redstoner-35/DFEx-FarBeaMon3tr/img/驱动仓去氧化后.jpg

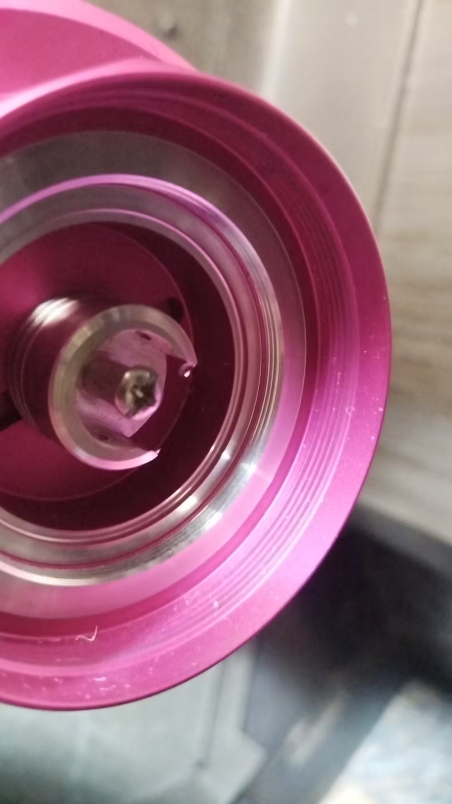
img/驱动仓去氧化后.jpg
