redstoner-35/DFEx-FarBeaMon3tr/机械/电池架/Step/电池架均衡和充电板空隙垫圈.STEP

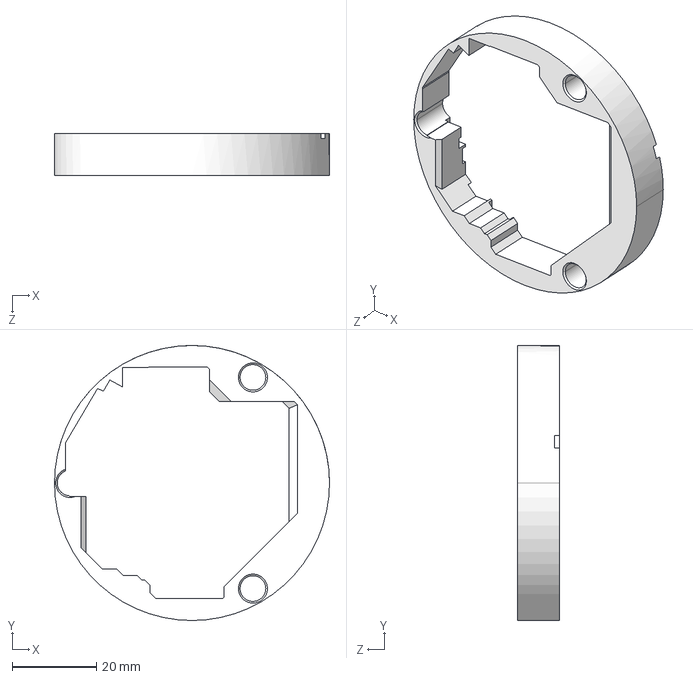
[picture p48: CAD file, 2025-11-03]
机械/电池架/Step/电池架均衡和充电板空隙垫圈.STEP
65.4 x 65.4 x 10.0 mm
