redstoner-35/DFEx-FarBeaMon3tr/机械/电池架/电池架正极黄铜导电电极.SLDPRT

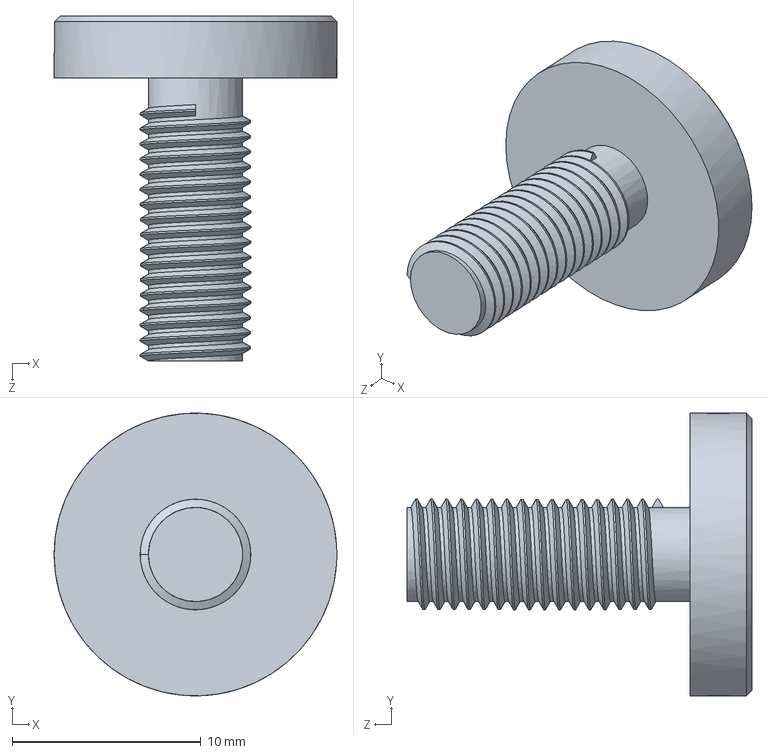
[picture p49: CAD file, 2025-05-08]
机械/电池架/电池架正极黄铜导电电极.SLDPRT
15.0 x 15.0 x 18.3 mm
