redstoner-35/DFEx-FarBeaMon3tr/机械/筒身/Step/电池仓尾盖.stp

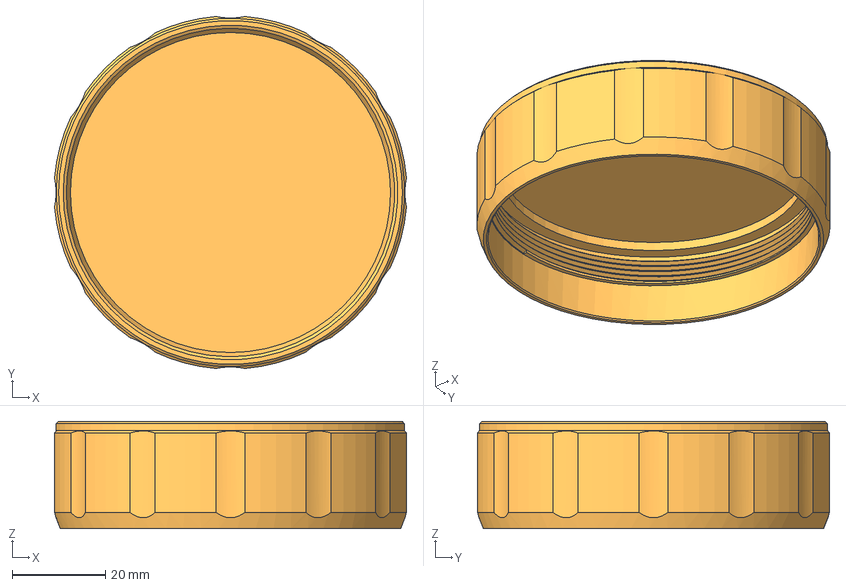
[picture p50: CAD file, 2025-05-15]
机械/筒身/Step/电池仓尾盖.stp
75.4 x 75.4 x 23.0 mm
