redstoner-35/DFEx-FarBeaMon3tr/机械/光学部分/定位片3D制造文件/专用定位片-7070灯珠.3mf

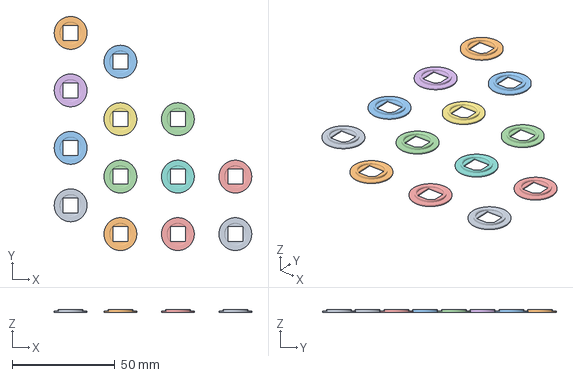
[picture p52: CAD file, 2025-07-03]
机械/光学部分/定位片3D制造文件/专用定位片-7070灯珠.3mf
96.2 x 114.0 x 1.50 mm
专用定位片-7070-PA6GF.STEP x 13
