redstoner-35/DFEx-FarBeaMon3tr/机械/电池架/Step/电池正极铜垫片.STEP

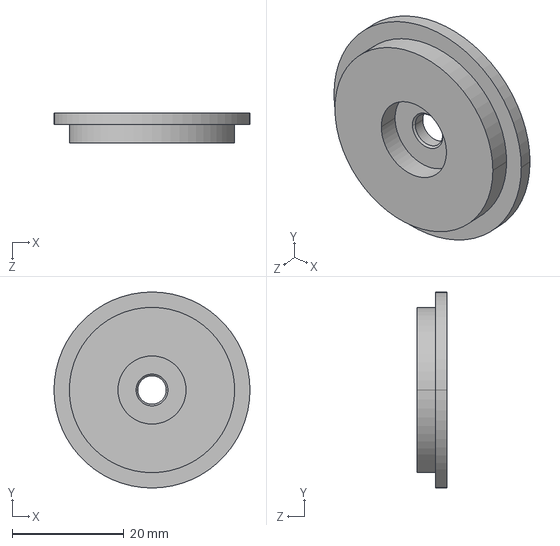
[picture p53: CAD file, 2025-11-03]
机械/电池架/Step/电池正极铜垫片.STEP
35.1 x 35.1 x 5.40 mm
