redstoner-35/DFEx-FarBeaMon3tr/机械/电池架/电池架装配效果.SLDPRT

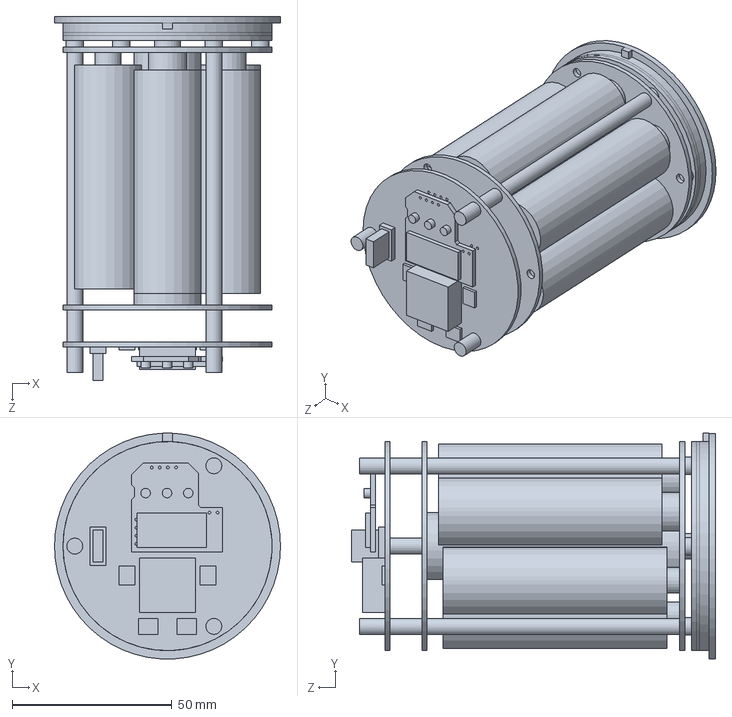
[picture p54: CAD file, 2025-05-08]
机械/电池架/电池架装配效果.SLDPRT
70.7 x 70.6 x 113.9 mm
