redstoner-35/DFEx-FarBeaMon3tr/机械/筒身/Step/电池仓前盖.stp

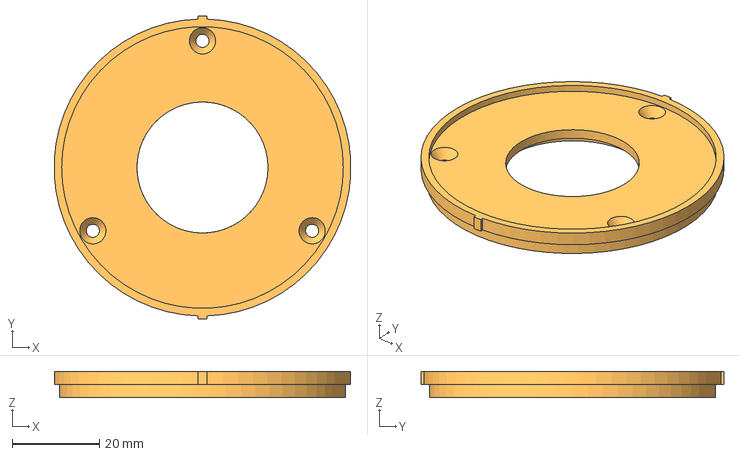
[picture p55: CAD file, 2025-05-15]
机械/筒身/Step/电池仓前盖.stp
67.9 x 69.4 x 6.00 mm
