redstoner-35/DFEx-FarBeaMon3tr/机械/风扇手柄外框/Step/40风扇不锈钢夹片-改版.STEP

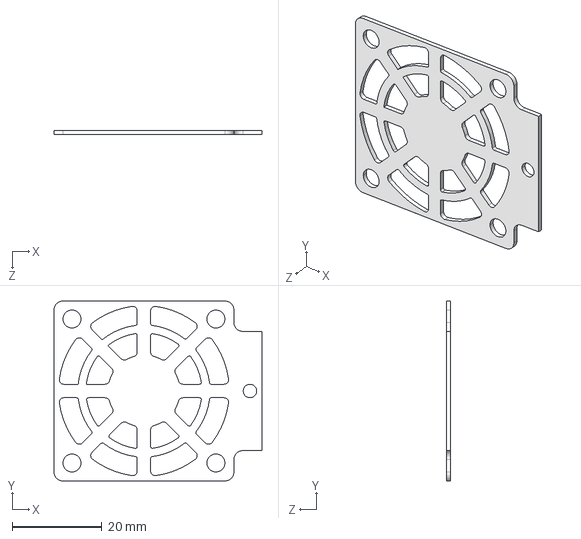
[picture p56: CAD file, 2025-11-03]
机械/风扇手柄外框/Step/40风扇不锈钢夹片-改版.STEP
46.2 x 40.0 x 1.00 mm
