redstoner-35/DFEx-FarBeaMon3tr/机械/筒身/Step/电池仓尾部显示面板.stp

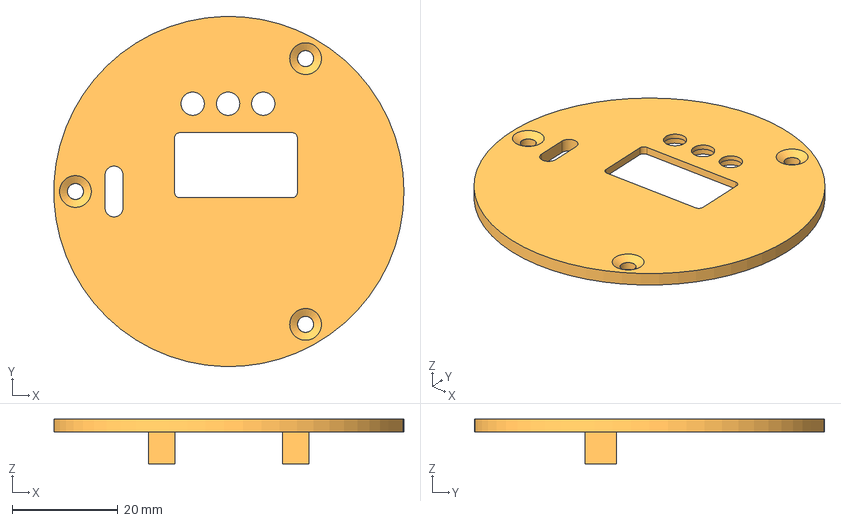
[picture p57: CAD file, 2025-05-15]
机械/筒身/Step/电池仓尾部显示面板.stp
66.2 x 66.2 x 8.50 mm
