redstoner-35/DFEx-FarBeaMon3tr/机械/风扇手柄外框/Step/40风扇外框23日.STEP

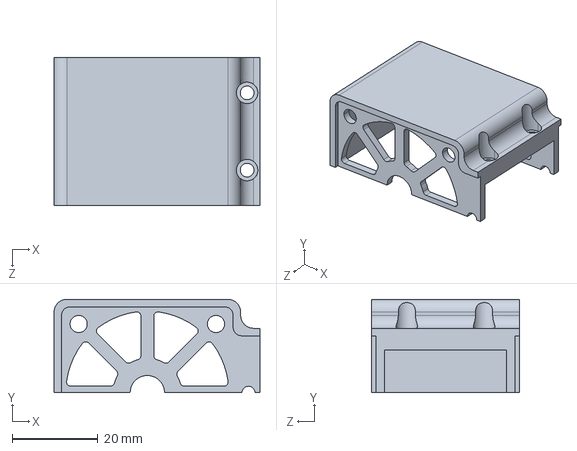
[picture p58: CAD file, 2025-11-03]
机械/风扇手柄外框/Step/40风扇外框23日.STEP
48.0 x 21.8 x 34.5 mm
