redstoner-35/DFEx-FarBeaMon3tr/机械/电池架/Step/电池架中心柱.STEP

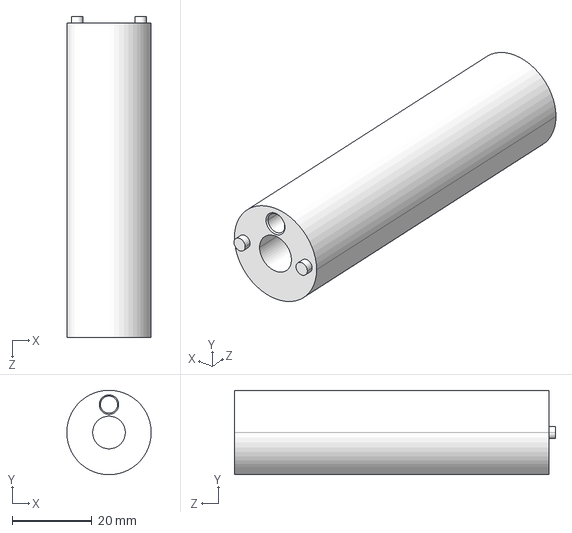
[picture p59: CAD file, 2025-05-08]
机械/电池架/Step/电池架中心柱.STEP
21.2 x 21.2 x 80.6 mm
