redstoner-35/DFEx-FarBeaMon3tr/固件/电池棒控制器固件/User/main.c

#include "ht32.h"
#include "delay.h"
#include "LCD_Init.h"
#include "lcd.h"
#include "ADC.h"
#include "I2C.h"
#include "Key.h"
#include "GUI.h"
#include "Config.h"
#include "CapTest.h"
#include "LogSystem.h"
#include "WatchDog.h"
#include "BalanceMgmt.h"
#include "AUXPSU.h"

//函数声明
void PowerMgmtSetup(void);
void KickIP2366ToWakeUp(void);
void IP2366_PreInit(void);
void IP2366_Telem(void);
void IP2366_PostInit(void);
void UpdateIfSysCanOFF(void);
void DetectIfIP2366Reset(void);
void EnteredInstantCapTest(void);
void PowermanagementSleepControl(void);
void CTestAverageACC(void);
void CTestFSMHandler(void);
void SysOverHeatProt(void);
void TCResetFSM(void);
void ApplyScreenDirection(void);
void IP2366_ReConfigOutWhenTypeCOFF(void);
void CheckForFlashLock(void);
void SetDebugPortState(bool IsEnable);
void AttackTimeCounter(void);
void PushDefaultResultToVBat(void);
void OverChargeDetectModule(void);
void HPPowerGuage_Start(void);
void AutoBalTIMHandler(void);
void AdapEmuTIMHandler(void);
void SysAutoSavePowerCfg(void);
void DynamicUpdateSinkPower(void);

//常量
bool SensorRefreshFlag=false;

int main(void)
 {
 //初始化系统时钟
 CKCU_PeripClockConfig_TypeDef CLKConfig={{0}};
 CLKConfig.Bit.PA=1;
 CLKConfig.Bit.PB=1;
 CLKConfig.Bit.PC=1;
 CLKConfig.Bit.AFIO=1;
 CLKConfig.Bit.ADC=1;
 CLKConfig.Bit.EXTI=1;
 CLKConfig.Bit.SPI0 = 1;
 CLKConfig.Bit.PDMA = 1;
 CLKConfig.Bit.WDT = 1;
 CLKConfig.Bit.BKP = 1;
 CKCU_PeripClockConfig(CLKConfig,ENABLE);
 //启动SYSTICK和电源锁定引脚
 #ifndef EnableDebugMode
 SetDebugPortState(false);
 #endif
 delay_init(); //对延时函数的运行环境进行初始化 
 PowerMgmtSetup(); //进行自举
 //底层外设初始化
 LCD_HardwareInit();
 LCD_Init(); //进行LCD的硬件初始化和寄存器初始化
 PostScreenInit(); //显示自检的初始主界面
 LCD_EnableBackLight(); //启动LCD背光，LCD开始显示
 //开始图形化自检
 EnableHBTimer(); //初始化系统8Hz心跳定时器
 SideKey_Init(); //侧按初始化 	
 InternalADC_Init(); //ADC初始化 
 KickIP2366ToWakeUp(); //踢一脚2366唤醒
 SMBUS_Init(); //启动SMBUS
 IP2366_PreInit(); //进行2368初步配置关闭充放电，读取寄存器后再开
 LoadConfig(); //读取系统配置
 CheckIfHBTIMStart(); //检查心跳定时器是否启动
 CheckForFlashLock(); //给存储器上锁永久禁止读取
 POR_ReadCapData(); //读取测容数据
 BalanceMgmt_Init(); //配置均衡控制器
 RunLogModule_POR(); //读取数据
 ApplyScreenDirection(); //应用屏幕方向
 IP2366_PostInit(); //IP2366应用后配置
 HPPowerGuage_Start(); //初始化高精度功率计
 PushDefaultResultToVBat(); //将电池电压数据默认应用给结构体进行显示
 EnteredInstantCapTest(); //尝试进入测试菜单
 AUXPSU_DetectIfCPortTriggerPresent(); //检测C口诱骗硬件是否存在
 //自检完毕，进入系统
 ShowPostInfo(100,"系统初始化完成",(char *)QueryPostDoneID(),Msg_POSTOK);
 delay_ms(!CfgData.EnableFastBoot?400:150); //关闭快速启动则多延时一会让人可以看清
 ClearScreen();
 //根据设置，执行菜单切换
 if(CfgData.InstantCTest==InstantCTest_EnteredOK)SwitchingMenu(&CapTestMenu); //一次性测容条件满足直接进入测容菜单
 else SwitchingMenu(CfgData.EnableLargeMenu?&LargeMainMenu:&MainMenu);        //否则切换到主菜单
 SensorRefreshFlag=false; //清除flag
 #ifndef EnableDebugMode
 WatchDog_Init(); //启动看门狗
 #endif
 //主循环
 while(1)
   {
	 //实时处理任务
	 ADC_GetResult(); 
	 SideKey_LogicHandler(); 
	 CTestFSMHandler(); //测容状态机处理
	 PowermanagementSleepControl(); //睡眠管理
	 SysOverHeatProt(); //过热保护处理
	 MenuRenderProcess(); //执行菜单渲染 
	 //125ms定时处理的入口和喂狗检测
	 if(!SensorRefreshFlag)continue;
	 #ifndef EnableDebugMode
	 WatchDog_Feed(); //喂狗
	 #endif
	 //进行其余125ms定时处理
	 AutoBalTIMHandler(); //自动均衡计时器
	 Balance_IOMgmt(); //进行均衡器的控制
	 SideKey_TIMCallback(); 
	 DynamicUpdateSinkPower(); //动态更新输入功率
	 UpdateIfSysCanOFF(); //更新系统是否可以关闭
	 IP2366_Telem(); //每0.125秒获取一次2366的状态
	 CTestAverageACC(); //测容系统遥测
	 UpdataRunTimeLog(); //更新日志
	 SysAutoSavePowerCfg(); //自动省电功能
	 OverChargeDetectModule(); //过充检测
	 DetectIfIP2366Reset(); //监测IP2366是否复位
	 GUIDelayHandler(); //GUI延时处理
	 AdapEmuTIMHandler(); //适配器模拟计时器处理
	 IP2366_ReConfigOutWhenTypeCOFF(); //从VBUS起来的重新连接
	 AUXPSU_Mgmt(); //进行辅助电源的配置
	 IntEditMenuKeyEffHandler(); //实现按下特效
	 TCResetFSM(); //实现Type-C重连
	 AttackTimeCounter(); //防止爆破攻击的保护
	 SensorRefreshFlag=false;
	 }
 return 0;
 }
