redstoner-35/DFEx-FarBeaMon3tr/固件/电池棒控制器固件/POST/IP2366_Init.c

#include "IP2366_REG.h"
#include "lcd.h"
#include "GUI.h"
#include "Config.h"
#include "delay.h"
#include "ADC.h"
#include "BalanceMgmt.h"
#include <string.h>
#include <math.h>
#include "AUXPSU.h"
#include "WatchDog.h"
#include "LogSystem.h"

typedef enum
	{
	IP2366DCState_Normal,
	IP2366DCState_LowTemp,
	IP2366DCState_highTemp
	}IP2366DCStateDef;

bool IsEnableDischargeAtStor=true;
static char WaitAfterTypeCRemoved;	
bool CurrentStorDisState=true;
bool IsSystemOverheating=false;
bool IsSystemLowTemp=false;
static IP2366DCStateDef IP2366DCDCState=IP2366DCState_Normal;
static bool IsAutoSaveEnabled=false;
static unsigned char AutoSavePowerTIM=160;
static unsigned char WaitTCReconnectTIM=0;
static unsigned int TCShortDisBlankTIM=0;
static bool IsSinkPowerThermalLimited;
static bool SysChgState; //系统充电状态
static ChargePowerDef CurrentSinkPower;  //当前系统的输入功率
IP2366ResetCPortProcDef IPSinkState=IP2366_CPort_Reseted;

//外部函数
void Force2366ToRestart(void); //强制2366断电重启

//计算存储模式开启时，是否打开放电模块
bool IP2366_IsEnableDischarge(float VBatRaw)
	{
	float VBatt,VbattThres;
	//计算电池电压
  VBatt=VBatRaw/BattCellCount;
	VBatt*=1000; //转mV
	//计算触发阈值
	VbattThres=3500+((float)StorageMode*100);
	//进行施密特处理
  if(VBatt>VbattThres+100)IsEnableDischargeAtStor=true;
	else if(VBatt<=VbattThres)IsEnableDischargeAtStor=false;
	//返回结果
	return IsEnableDischargeAtStor;
	}	

//内部函数，负责根据系统当前温度运算充电功率
bool UpdateSinkPower(bool IsForceUpdate)
	{
	ChargePowerDef Buf;
	//系统不支持返回true
	if(!CurrentIP2366FW->ExtendedTCSetting)return true;
	//关闭输入自适应Sink功能，强制使用指定的Sink Power
	if(!CfgData.EnableSmartSinkPower)Buf=CfgData.MaxSnkPower;
	//温度监视系统故障，使用最低的充电功率
	else if(!ADCO.IsNTCOK)Buf=Power_30W;
	//温度监视系统正常，按照温度值选择充电功率
	else if(ADCO.Systemp<42)Buf=Power_140W;
	else if(ADCO.Systemp<45)Buf=Power_100W;
	else if(ADCO.Systemp<48)Buf=Power_65W;
	else if(ADCO.Systemp<52)Buf=Power_60W;
	else if(ADCO.Systemp<55)Buf=Power_45W;
	else Buf=Power_30W;
	//判断当前系统设置是否小于算出来的充电功率，如果小于则override为系统设置
	if(Buf>CfgData.MaxSnkPower)Buf=CfgData.MaxSnkPower;
	if(IsForceUpdate||CurrentSinkPower!=Buf)	
		{
		//设置充电功率寄存器，成功则同步结果并返回true，否则返回false
		if(IP2366_UpdateSinkPower(Buf))CurrentSinkPower=Buf;
		else return false; 
		}
	//其余情况，返回true
  return true;
	}	
	
//如果系统因为充电开始时过温限制了充电功率，则该模块会尝试在系统回到低温状态后恢复充电功率
void RestoreSinkPower(void)
	{
	float Thres;
	//当前没有使能升功率操作	
	if(!IsSinkPowerThermalLimited)return;
	//根据目标的Sink Power判断触发回升的阈值
	switch(CfgData.MaxSnkPower)
		{
		case Power_140W:Thres=42;break;
		case Power_100W:Thres=45;break;
		case Power_65W:Thres=48;break;
		case Power_60W:Thres=52;break;
		case Power_45W:Thres=55;break;
		case Power_30W:Thres=60;break;
		}
	//如果当前系统温度小于回升阈值，则触发回升
	if(!ADCO.IsNTCOK||ADCO.Systemp>=Thres)return;
	if(UpdateSinkPower(true))IsSinkPowerThermalLimited=false;
	}	
	
//在连接C口后，动态更新输入最大功率
void DynamicUpdateSinkPower(void)
	{
	bool Result;
	BatteryStateDef BattState;
	//系统不支持单独设置Sink输入或者关闭了智能功率协商，不执行
  if(!CurrentIP2366FW->ExtendedTCSetting||!CfgData.EnableSmartSinkPower)return;		
	//检测系统是否连接输入且处于正在充电过程中
	if(!IP2366_GetIfInputConnected())Result=false;
	else if(!IP2366_GetChargerState(&BattState))Result=false;
	else switch(BattState)
		{
		case Batt_ChgWait:
		case Batt_CCCharge:
		case Batt_CVCharge:Result=true;break;
	  //其余情况
		default:Result=false;
		}	
	//C口处于插入状态，执行恢复输入功率的尝试
	if(Result)RestoreSinkPower();
	//定时器递减
	else if(TCShortDisBlankTIM>0)TCShortDisBlankTIM--;
	//检测到用户插入C口后更新充电功率
  if(SysChgState==Result)return;	
	//当前系统拔除C口，不执行充电功率更新，进入消隐阶段短时间内阻止C口断联引起的误判
	if(TCShortDisBlankTIM||!Result)
		{
		TCShortDisBlankTIM=480;
		SysChgState=Result;
		}		
	else 
		{
	  //正常执行更新事件并判断输入功率是否被限制
		if(UpdateSinkPower(false))SysChgState=Result;
	  if(CurrentSinkPower<CfgData.MaxSnkPower)IsSinkPowerThermalLimited=true;
		else IsSinkPowerThermalLimited=false;
		}
	}
	
//IP2366初始化
void IP2366_PreInit(void)
	{
	char i=5;
	char VendorString[6];
	char FWIDReport[32];
	IP2366InputDef ICFG;
	IP2366OutConfigDef OCFG;
	IP2366HWRevDef HWID;
	ShowPostInfo(25,"充电IC初配置","07",Msg_Statu);
	//配置结构体
	ICFG.ChargeCurrent=9700;
	ICFG.ChargePower=Power_100W;
	ICFG.FullVoltage=4200;
	ICFG.PreChargeCurrent=200;
	ICFG.IsEnableCharger=false;
		
	OCFG.IsEnableDPDMOut=false;
  OCFG.IsEnableOutput=false;
  OCFG.IsEnablePDOut=false;
  OCFG.IsEnableSCPOut=false;		
	//监测是否存在
	do	
		{
		if(IP2366_DetectIfPresent())break;
		delay_ms(200);
		ShowPostInfo(25,"尝试连接至IC","W3",Msg_Warning);
		i--;
		}
	while(i>0);	
	//尝试了五次仍然失败，提示错误发送
	if(i==0)	
		{
		ShowPostInfo(25,"充电IC通信失败","E5",Msg_Fault);
		SelfTestErrorHandler();
		}
	
	//监测Type-C状态
  if(!IP2366_GetIfInputConnected())
		{
		//输入未连接，禁止输入输出
		IP2366_SetOutputState(&OCFG); //禁用输出		
		IP2366_SetInputState(&ICFG,true);
		}
	//禁止充电器工作
	else IP2366_DisableCharger();	
		
	//读取芯片并且进行比对，比对的同时更新芯片capability set
	ShowPostInfo(25,"充电IC版本检查","08",Msg_Statu);
	memset(VendorString,0,sizeof(VendorString));    
	if(!IP2366_GetFirmwareTimeStamp(VendorString))		
		{
		ShowPostInfo(79,"读取固件版本失败\0","E6",Msg_Fault);
		SelfTestErrorHandler();
		}		
	if(!IP2366_UpdateChipCap(VendorString))
		{
		memset(FWIDReport,0,sizeof(FWIDReport));
		snprintf(FWIDReport,sizeof(FWIDReport),"固件ID:%s",VendorString);
		ShowPostInfo(79,FWIDReport,"E7",Msg_Fault);
		delay_Second(1);
		ShowPostInfo(79,"不受支持的固件版本\0","E7",Msg_Fault);
		SelfTestErrorHandler();	
		}
	//如果芯片支持读取硬件版本，则读取芯片的硬件版本并进行比对
	if(!CurrentIP2366FW->ExtendedROREGCapable)return;
	HWID=IP2366_GetChipHWRev();
	if(HWID!=Hardware_Ver_D)
		{
		if(HWID==Hardware_Ver_Unknown)ShowPostInfo(79,"读取芯片版本失败\0","E6",Msg_Fault);
		else ShowPostInfo(79,"不受支持的硬件版本\0","E7",Msg_Fault); 
		SelfTestErrorHandler();
		}
	}
	
//内部函数，进行充放电功率的降档
static void DischargeStepDown(void)
	{
	if(CfgData.InputConfig.ChargePower==Power_140W)CfgData.InputConfig.ChargePower=Power_100W;
	else CfgData.InputConfig.ChargePower=Power_65W;
	}	
	
static void ChargeStepDown(void)
	{
	if(CfgData.MaxSnkPower==Power_140W)CfgData.MaxSnkPower=Power_100W;
	else CfgData.MaxSnkPower=Power_65W;
	}
	
//获取系统的充放电和C口角色状态
static void QuerySystemChargeState(bool *ChgState,bool *DisState,TypeCRoleDef *TCRole)
	{
	extern bool IsEnableAdapterEmu;
	extern bool IsEnableTempChargeOnly;
	extern AutoBalanFSMDef AutoBalState;
	extern bool IsCPortBreaked;
	//内部buffer	
	bool ChgEN,DisEN;
	TypeCRoleDef Role;		
	//计算DCDC使能状态
	if(BalanceForceEnableTIM>0||AutoBalState==AutoBalance_RunningBalance)	
		{
		//手动均衡运行中，关闭充放电
		ChgEN=false;
		DisEN=false;
		if(IsCPortBreaked)Role=TypeC_NoConnect; 		 //C口被打断之后禁止充电，强制断开source
		else Role=TypeC_SinkOnly;                    //开启充电功能
		}
	else if(IsSystemOverheating)
		{
		//系统过热，关闭充放电
		ChgEN=false;
		DisEN=false;
		Role=TypeC_NoConnect;
		}	
	else if(IsEnableAdapterEmu)
		{
		//开启适配器模拟，开启放电关闭充电
		ChgEN=false;
		DisEN=true;
		Role=TypeC_SourceOnly;
		}	
	else
		{
		ChgEN=IsSystemLowTemp?false:true;      //如果系统处于低温保护，则禁止充电
		if(IsEnableTempChargeOnly)DisEN=false; //临时打开仅充电功能
		else if(StorageMode!=StorageMode_OFF)DisEN=IP2366_IsEnableDischarge(ADCO.Vbatt);  //存储模式开启，使用当前电池电压进行配置是否使能放电
		else DisEN=DCDCOutputBit;
		Role=DisEN?TypeC_Bidir:TypeC_SinkOnly; //根据输出是否启用配置角色为DRP或者DFP
		}		
	//数值计算结束，赋值到上一级函数的buffer里面去
  if(ChgState!=NULL)*ChgState=ChgEN;
	if(DisState!=NULL)*DisState=DisEN;
	if(TCRole!=NULL)*TCRole=Role;
	}
	
//设置系统的充放电使能和typec角色
bool SetSystemDischargeState(void)
	{
	bool ChgEN,DisEN;
	TypeCRoleDef Role;		
  BatteryStateDef BattState;
	bool IsStepDown;
	//判断过热保护是否满足条件
	if(!IsSystemOverheating)IsStepDown=false;                    //过热保护未触发
	else if(!CfgData.EnableThermalStepdown)IsStepDown=false;
	else if(CfgData.InputConfig.ChargePower>Power_65W)IsStepDown=true;
	else 
		{
		//根据充电功率判断是否满足掉档
		if(!CurrentIP2366FW->ExtendedTCSetting)IsStepDown=false;
		else if(CfgData.MaxSnkPower>Power_65W)IsStepDown=true;
		else IsStepDown=false;
		}	
	//过热保护使能，触发保护机制
	if(IsStepDown)
		{	
		//支持单独设置输出输入功率的固件，根据当前是充电还是放电，减少对应的功率值	
		if(CurrentIP2366FW->ExtendedTCSetting)
			{
			//获取电池状态
			BattState=Batt_StandBy;
			IP2366_GetChargerState(&BattState);
      switch(BattState)
				{
				case Batt_discharging:
					//放电模式只降放电功率
					DischargeStepDown();
					break;
				case Batt_StandBy:
					//状态获取失败，全部降
					ChargeStepDown();
					DischargeStepDown();
					break;
				default:
					//其余情况是充电，只降充电
					ChargeStepDown();
					break;
				} 
			}
		//不支持单独充放电设置的固件，同步一起降档
		else ChargeStepDown();
		//保存配置并更新sink和充电功率
		WriteConfiguration(&CfgUnion,false);
		DynamicUpdateSinkPower();
		if(!IP2366_UpdataChargePower(CfgData.InputConfig.ChargePower))return false;	
		}
	//设置C口角色
	QuerySystemChargeState(&ChgEN,&DisEN,&Role); //进行运算得出C口和充放电使能结果
	if(!IP2366_EnableDCDC(ChgEN,DisEN))return false;
	if(!IP2366_SetTypeCRole(Role))return false;
	//设置成功
	return true;
	}	
	
//存储模式使能放电管理的处理
static void StorageModeDischargeControl(void)
	{
	bool DischargeState;
	extern bool IsEnableAdapterEmu;
	//存储模式关闭，或者不执行检测
	if(StorageMode==StorageMode_OFF)return;
	//开启存储模式，进行检测
	DischargeState=IP2366_IsEnableDischarge(ADCO.Vbatt);
	if(IsEnableAdapterEmu)	
		{
		//适配器模拟模式下，不允许执行下面的重新初始化动作
		CurrentStorDisState=DischargeState;
		return;
		}
	if(CurrentStorDisState==DischargeState)return;
  if(SetSystemDischargeState())CurrentStorDisState=DischargeState;
	}	

//在电池充满电后20秒自动关闭输入快充协议，使充电器进入低功耗待机的功能
bool GetIfCapTestRunning(void);	
	
void SysAutoSavePowerCfg(void)
	{
	BatteryStateDef BattState;
	IP2366SinkProtocolDef PROTBuf;
	extern bool IsAutoBalRunning;
	bool QCDISEnabled,ForceRefresh=false;
	//当前处于自动均衡模式，关闭自动省电功能	
	if(IsAutoBalRunning)QCDISEnabled=false;
	//开启省电模式,未处于测容状态且当前2366固件支持省电模式，自动读取充电状态
	else if(!GetIfCapTestRunning()&&CfgData.EnableAutoPowerSave&&CurrentIP2366FW->ExtendedTCSetting)
		{
		if(!IP2366_GetChargerState(&BattState))return;
		switch(BattState)
			{
			case Batt_StandBy:
				 if(WaitTCReconnectTIM==1)
					 {
					 ForceRefresh=true;
					 IPSinkState=IP2366_CPort_Reseted; //C口拔除超过5秒，强制Clear输出等待状态机并恢复到初始状态
					 WaitTCReconnectTIM=0;
					 }
				 else	WaitTCReconnectTIM--;
				 //始终维持住false，Clear掉结果
				 QCDISEnabled=false;
				 break;
			case Batt_ChgDone:
			case Batt_ChgError:QCDISEnabled=true;break;
			//其余情况关闭快充
			default:QCDISEnabled=false;
			}
		}
	//关闭省电模式，始终开启协议
	else QCDISEnabled=false;
	//设置计时器
	if(!QCDISEnabled)AutoSavePowerTIM=160;
	else if(AutoSavePowerTIM)AutoSavePowerTIM--; //倒计时
	//检测计时器状态
	QCDISEnabled=AutoSavePowerTIM?false:true;
	if(!ForceRefresh&&IsAutoSaveEnabled==QCDISEnabled)return; //不需要更改
	//设置输入协议
	switch(IPSinkState)
		{
		case IP2366_CPort_Reseted:  //当前IP2366的C口处于标准协议支持状态，关闭支持的协议
			//关闭所有协议
			PROTBuf.EnableSinkDPDM=QCDISEnabled?false:CfgData.SinkConfig.EnableSinkDPDM;
			PROTBuf.EnableSinkPD=QCDISEnabled?false:CfgData.SinkConfig.EnableSinkPD;
			PROTBuf.EnableSinkSCP=QCDISEnabled?false:CfgData.SinkConfig.EnableSinkSCP;		
			if(IP2366_SetSinkProtocol(&PROTBuf))IsAutoSaveEnabled=QCDISEnabled;
		  else break;
		  if(IsAutoSaveEnabled)
				{
				WaitTCReconnectTIM=49; //等待6秒时间
				IPSinkState=IP2366_CPort_WaitNextFullCharge; //进入等待下一轮的状态
				}
			break;
		case IP2366_CPort_WaitNextFullCharge: //等待下一次充满
			IsAutoSaveEnabled=QCDISEnabled;
			if(QCDISEnabled)IPSinkState=IP2366_CPort_NextChargeDone;
		  break;
		case IP2366_CPort_NextChargeDone:	//下次已充满，复位
			IsAutoSaveEnabled=QCDISEnabled;
			if(!QCDISEnabled)WaitTCReconnectTIM=1;  //充满之后重置FSMTIM=1，让C口拔掉之后立马恢复正常
		  break;			
		}		
	}	
	
//系统过热保护处理	
void SysOverHeatProt(void)
	{
	IP2366DCStateDef StateBuf;
  //执行存储模式管理和自循环管理
	StorageModeDischargeControl();
	//NTC异常
	if(!ADCO.IsNTCOK)return;
	//检测是否低温	
	if(ADCO.Systemp<=0)IsSystemLowTemp=true;
	else if(ADCO.Systemp>15)IsSystemLowTemp=false;
	//检测是否过热	
	if(ADCO.Systemp>(float)CfgData.OverHeatLockTemp)IsSystemOverheating=true;
	else if(ADCO.Systemp<(float)CfgData.OverHeatLockTemp-10)IsSystemOverheating=false;			
	//计算并同步DCDC状态
	if(IsSystemOverheating)StateBuf=IP2366DCState_highTemp;
	else if(IsSystemLowTemp)StateBuf=IP2366DCState_LowTemp;
	else StateBuf=IP2366DCState_Normal;
	
  if(IP2366DCDCState==StateBuf)return;
	if(SetSystemDischargeState())IP2366DCDCState=StateBuf;
	}	
	
//进行IP2366的输出初始化	
static bool IP2366_InitOutputSystem(bool StorageInput)
	{
	IP2366OutConfigDef OCFG;
	extern bool IsEnableTempChargeOnly;
	//设置协议
	OCFG.IsEnableDPDMOut=CfgData.OutputConfig.IsEnableDPDMOut;
	OCFG.IsEnableHSCPOut=CfgData.OutputConfig.IsEnableHSCPOut;
	OCFG.IsEnablePDOut=CfgData.OutputConfig.IsEnablePDOut;
	OCFG.IsEnableSCPOut=CfgData.OutputConfig.IsEnableSCPOut;
	if(IsEnableTempChargeOnly)OCFG.IsEnableOutput=false;
	else if(StorageMode!=StorageMode_OFF)
			OCFG.IsEnableOutput=StorageInput; //调用输出配置函数检测电池电压状态
	else 
			OCFG.IsEnableOutput=DCDCOutputBit;
	//写寄存器设置输出模块	
	return IP2366_SetOutputState(&OCFG);
	}	
	
//计算系统是否开启DCDC输出
bool CalcIfDCDCOutEnabled(void)
	{
	extern bool IsEnableAdapterEmu;
	extern bool IsEnableTempChargeOnly;
	//根据系统状况返回DCDC输出使能值
	if(IsSystemOverheating||IsEnableTempChargeOnly)return false;
	else if(IsEnableAdapterEmu)return true;
	else if(StorageMode!=StorageMode_OFF)return CurrentStorDisState;  //存储模式开启，使用当前电池电压进行配置
	//其余情况，返回系统输出bit
	return DCDCOutputBit;
	}
	
//根据系统配置重新初始化2366
void IP2366_ReInitBasedOnConfig(void)
	{
	IP2366InputDef ICFG;
	IP2366OutConfigDef OCFG;
	IP2366SinkProtocolDef PROTBuf;
	bool DisableSinkFChg;	
	bool ChgEN,DisEN;
	TypeCRoleDef Role;		
	//外部参考	
	extern bool OCState;
	extern bool IsCPortBreaked;
	//获取一边系统基础参数
  QuerySystemChargeState(&ChgEN,&DisEN,&Role);		
		
	//设置低电保护、PDO参数和输出参数
	OCFG.IsEnableDPDMOut=CfgData.OutputConfig.IsEnableDPDMOut;
	OCFG.IsEnablePDOut=CfgData.OutputConfig.IsEnablePDOut;
	OCFG.IsEnableSCPOut=CfgData.OutputConfig.IsEnableSCPOut;
	OCFG.IsEnableHSCPOut=CfgData.OutputConfig.IsEnableHSCPOut;
	if(!DisEN)OCFG.IsEnableOutput=false;
	else OCFG.IsEnableOutput=CalcIfDCDCOutEnabled();
	
	IP2366_SetVLowVolt(CfgData.Vlow);
	if(!IsBootFromVBUS&&!OCState)IP2366_SetOutputState(&OCFG);	//如果是在过充阶段或者是单独插着Type-C，那就不能设置输出，不然单片机直接断电了
	IP2366_SetPDOBroadCast(&CfgData.PDOCFG);
	//设置输入参数
	switch(StorageMode)
		{
		//根据存储模式配置输出
		case StorageMode_OFF:ICFG.FullVoltage=CfgData.InputConfig.FullVoltage;break; //存储模式禁用,使用系统设置的最高电压
		case StorageMode_3V6:ICFG.FullVoltage=3600;break; //存储模式启用，电池最大电压3.6V
		case StorageMode_3V7:ICFG.FullVoltage=3700;break; //存储模式启用，电池最大电压3.7V
	  case StorageMode_3V8:ICFG.FullVoltage=3800;break;	//存储模式启用，电池最大电压3.8V
		}		
	ICFG.ChargePower=CfgData.InputConfig.ChargePower;	
	ICFG.PreChargeCurrent=CfgData.InputConfig.PreChargeCurrent; //其他参数照常填写
	ICFG.IsEnableCharger=ChgEN; 															  //根据运算结果选择充电i是否开启
	//根据系统配置设置是否禁用Sink协议
	if(IsCPortBreaked)DisableSinkFChg=true; //C口被打断，强制禁用
	else if(CfgData.EnableAutoPowerSave)DisableSinkFChg=IPSinkState==IP2366_CPort_Reseted?false:true;		
	else DisableSinkFChg=false; //默认情况下Sink快充开启
	//配置具体的协议项
	PROTBuf.EnableSinkDPDM=DisableSinkFChg?false:CfgData.SinkConfig.EnableSinkDPDM;
	PROTBuf.EnableSinkPD=DisableSinkFChg?false:CfgData.SinkConfig.EnableSinkPD;
	PROTBuf.EnableSinkSCP=DisableSinkFChg?false:CfgData.SinkConfig.EnableSinkSCP;		
	IP2366_SetSinkProtocol(&PROTBuf);	
	//设置充电系统参数以及ICCMAX
	if(CfgData.MaxSnkPower<CurrentSinkPower)CurrentSinkPower=CfgData.MaxSnkPower; //检测充电系统是否下调功率
	IP2366_UpdateSinkPower(CurrentSinkPower);  //根据当前的充电功率，更新Sink功率到额定值
	ICFG.ChargeCurrent=OCFG.IsEnableOutput?CurrentIP2366FW->IP2366ICCMAX:CfgData.InputConfig.ChargeCurrent; //初始化时如果开启输出则按照固件能力填写
	IP2366_SetInputState(&ICFG,IsBootFromVBUS?false:true);	
	//设置PPS和fixed PDO参数
	IP2366_SetDeepSleepModeEnabled(CfgData.SleepCfg==System_Sleep_Deep?true:false);
	IP2366_SetFixedPDO(&CfgData.FixedPDOCfg);
	IP2366_SetPPSCurrent(&CfgData.PPSConfig);
	//设置Type-C模式
	if(!IsBootFromVBUS&&!OCState)IP2366_SetTypeCRole(Role); //如果是在过充阶段或者是单独插着Type-C，那就不能发送TCRST命令不然单片机直接断电了
  //设置OCP和清除OC Flag		
	IP2366_SetOTPSign();
	IP2366_ClearOCFlag(); //移除OC Flag
	}	

//根据配置动态计算和设置2366的限流以及浮充截止电压
void IP2366_SetIBatLIMBaseOnSysCfg(void)
	{
	int Current;
	VBatLowDef DesiredVlow;
	bool result;
	//根据系当前是否处于安全模式，从对应的函数取出充电结果	
	if(IsBootFromVBUS)result=GetIfVBUSHasSinkVolt();
	else result=IP2366_GetIfInputConnected();
	//设置低电压保护和预期浮充截止电压
	if(result)DesiredVlow=CfgData.PreChargeEndVoltage;   //充电模式连接，更新充电结果
	else DesiredVlow=CfgData.Vlow;    //放电模式使用低电压保护值
	//计算动态限流
	if(result)Current=CfgData.InputConfig.ChargeCurrent; //充电模式已连接，设置为充电限流
	else Current=CfgData.InputConfig.ChargeCurrent>CurrentIP2366FW->IP2366ICCMAX?CfgData.InputConfig.ChargeCurrent:CurrentIP2366FW->IP2366ICCMAX; //为了确保放电正常运行，当充电未接入时设置为9.7A限流(如果电池限流比这个大那就设置为9700)
	//设置ICCMAX寄存器	
	IP2366_SetICCMax(Current); 
	//设置Vlow寄存器实现可调涓流电压的功能
	IP2366_DynamicUpdateVlow(DesiredVlow);
	}
	
//尝试恢复IP2366
void IP2366StallRestore(void);
extern short IPStallTime;	
	
void DetectIfIP2366Reset(void)
	{
	bool Reset;
	//执行2366充电环卡死检测
	IP2366_LockUpDetect();
	//获取当前芯片通信状态
	if(!IP2366_DetectIfChipReset(&Reset))IP2366StallRestore(); //开始计时
	//芯片发生复位，重置寄存器
	else if(Reset)IP2366_ReInitBasedOnConfig(); //重新初始化
	else IPStallTime=0; //未发生复位
	//对输出电流进行应用
	if(!CalcIfDCDCOutEnabled())return; //输出被关闭不需要动态设置限流
  IP2366_SetIBatLIMBaseOnSysCfg(); //动态设置
	}

//如果存在电池，则在拔出TypeC之后的一段时间重新初始化
void IP2366_ReConfigOutWhenTypeCOFF(void)	
	{
	extern short VBUSReConnectTimeCounter;
	float PreChargeEndVBat;
	bool IsSystemCharging,IsAbleClearSafeMode;
	if(!IsBootFromVBUS)return;
	//判断系统是否连接了输入正在充电	
	IsSystemCharging=GetIfVBUSHasSinkVolt();
	//根据系统设置的涓流电压计算出退出安全模式，转高功率充电的电压值
	switch(CfgData.PreChargeEndVoltage)
		{
		case VLow_2V8:PreChargeEndVBat=2.8*BattCellCount;break;
		case VLow_2V9:PreChargeEndVBat=2.9*BattCellCount;break;
		case VLow_3V0:PreChargeEndVBat=3.0*BattCellCount;break;
		case VLow_3V1:PreChargeEndVBat=3.1*BattCellCount;break;
		case VLow_3V2:PreChargeEndVBat=3.2*BattCellCount;break;
		//其余非法值使用3.0	
		default: PreChargeEndVBat=3.0*BattCellCount;
		}
	//如果系统处于充电模式，则同时判断充电电流和电池电压是否达到要求
	if(IsSystemCharging)
		{
		//电池电压未达到转恒流点，保持安全模式
		if(ADCO.Vbatt<PreChargeEndVBat)IsAbleClearSafeMode=false;
		//电池电压达到3.5V每节，强制转全功率充电
		else if(ADCO.Vbatt>=(3.5*BattCellCount))IsAbleClearSafeMode=true;
		//电池电压达到转恒流点，判断系统是否真的正在充电
		else if(ADCO.Ibatt>0.2)IsAbleClearSafeMode=true;
		//其余情况，保持在安全模式
		else IsAbleClearSafeMode=false;
		}
	//系统处于待机或者放电，判断电压是否达到要求
	else IsAbleClearSafeMode=ADCO.Vbatt<(3.5*BattCellCount)?false:true;	

	//完成条件判断，根据条件是否满足定义计时器是否继续计时
  if(!IsAbleClearSafeMode)WaitAfterTypeCRemoved=50;
	else if(WaitAfterTypeCRemoved>0)WaitAfterTypeCRemoved--;
	else
		{
		if(GetIfCapTestRunning())VBUSReConnectTimeCounter=80; 	//系统即将从安全模式切换到正常充电，置位消隐定时器避免容量测试误认为C口被拔出
		IsBootFromVBUS=false;
		//关闭充电DCDC，并且设置为sink only，延时150mS
		IP2366_EnableDCDC(false,false);
	  AUXPSU_SetTypeCFVoutState(false);
		IP2366_SetTypeCRole(TypeC_SourceOnly);
		delay_ms(150);
		WatchDog_Feed();
		//令IP2366把继电器切换过去，然后重新连接到C扣
		AUXPSU_SetIPDState(true);
		AUXPSU_ConnectTCtoIP2366();		//充电达到足够时长之后切换回IP2366进行高功率充电
		delay_ms(150);
		IP2366_ReInitBasedOnConfig(); //重新初始化2366
		WatchDog_Feed();
		IP2366_SetTypeCRole(CalcIfDCDCOutEnabled()?TypeC_Bidir:TypeC_SinkOnly);
		}
	}
//在继电器切换CC pin之后等待芯片重新连接
static void IP2366_WaitChipInitAfterChangeCC(void)	
	{
	int i=40;
	do
		{
		if(IP2366_DetectIfPresent())return;
		delay_ms(100);
		}
	while(--i);
	//等待超时处理
	ShowPostInfo(25,"充电IC通信失败","E5",Msg_Fault);
	SelfTestErrorHandler();
	}

//后初始化
void IP2366_PostInit(void)
	{
	bool IsCmdSendOK;		
	extern bool EnableDetailOutput;
	bool Result;
	IP2366VBUSStateDef VBUSState;
	IP2366InputDef ICFG;	
	IP2366SinkProtocolDef SinkCFG;
	float VdroopRate;
	int retry=5,i;
	char VendorString[5];
	ShowPostInfo(78,"充电IC后配置\0","28",Msg_Statu);
	//检查系统是否由VBUS供电
	i=0;
  do
		{
		delay_ms(100);
		ADC_GetResult();
		VdroopRate=PORVBatVolt-ADCO.Vbatt; //计算电池电压变化
    if(PORVBatVolt<(2.50*BattCellCount))
			{
			i=10;
			break; //电池初始化时电压异常，报错
			}
		else if(VdroopRate<0.05)break;
		i++;
		}
	while(i<10);	
  if(i==10)//监测到电池异常，触发保护	
    {		
		ShowPostInfo(78,"电池电压异常\0","W8",Msg_Warning);
		delay_Second(1);
		ShowPostInfo(78,"电池是否正确安装?","W8",Msg_Warning);
		delay_Second(1);
		if(!IsBootFromVBUS)
			{
			//获取一遍VBUS电压
			IP2366_GetVBUSState(&VBUSState);
			
			RunLogEntry.LastDataCRC=CalcRunLogCRC32(&RunLogEntry.Data); //强制刷新旧日志的结果
			IsBootFromVBUS=true;
			RunLogEntry.CurrentDataCRC=CalcRunLogCRC32(&RunLogEntry.Data); //计算运行日志的CRC32
			ShowPostInfo(78,"系统将进入安全模式\0","W8",Msg_Warning);
			WriteRuntimeLogToROM(); //保存日志		
				
			//电池电量异常，此时系统进入Fail-Safe Boot模式，强制C口取电为系统供电	
			SinkCFG.EnableSinkDPDM=false;
      SinkCFG.EnableSinkPD=false;
      SinkCFG.EnableSinkSCP=false;				
			IP2366_SetSinkProtocol(&SinkCFG); //关闭所有C口协议
			IP2366_EnableDCDC(false,false);   //关闭充电器
			
			//充电器不太聪明，强制输出20V为了避免芯片充电拉爆，强制充电器reset然后掉回去5V
			retry=200;
			if(VBUSState.VBUSVolt>13.0)do
				{	
				delay_ms(30);
				//延迟30mS后获取VBUS电压
				IP2366_GetVBUSState(&VBUSState);
				if(VBUSState.VBUSVolt<6.0)break;
				//重试失败，等待结果
				retry--;
				}
			while(retry);
			//充电器成功降压，切换继电器到安全模式，并重启系统
			if(retry)
				{	
				//重置操作之前，启动看门狗防止系统电源不稳后MCU跑飞，无法复位导致无限黑屏						
				WatchDog_Init(); 				
				WatchDog_Feed();
					
				//发送命令切换磁保持继电器，切换至安全启动模式	
				ForceEnableAdvPM();	
				AUXPSU_SetIPDState(true);						
				AUXPSU_ConnectTCtoIPD();					
					
				//显示重置成功并重启系统	
				delay_Second(1);									
				ShowPostInfo(78,"充电器重置完毕\0","4A",Msg_Warning);
				delay_Second(1);
				NVIC_SystemReset();	
				}
			//充电器降压失败，报错
			ShowPostInfo(78,"充电器重置超时\0","FE",Msg_Fault);
			SelfTestErrorHandler();			
			}
		}
	else if(IsBootFromVBUS&&ADCO.Vbatt>(3.50*BattCellCount))
		{
		ShowPostInfo(78,"电池电压已恢复\0","49",Msg_INFO);
		delay_Second(1);
		ShowPostInfo(78,"系统将退出安全模式\0","49",Msg_INFO);
		RunLogEntry.LastDataCRC=CalcRunLogCRC32(&RunLogEntry.Data); //强制刷新旧日志的结果
		IsBootFromVBUS=false;	
		RunLogEntry.CurrentDataCRC=CalcRunLogCRC32(&RunLogEntry.Data); //计算运行日志的CRC32
		WriteRuntimeLogToROM(); //保存日志		
		ForceEnableAdvPM();
		AUXPSU_ConnectTCtoIP2366();	//令磁保持继电器将CC线连接到IP2366
		//等待芯片重新协商
		IP2366_WaitChipInitAfterChangeCC();
		}
	//低温保护
	if(ADCO.IsNTCOK&&ADCO.Systemp<=0)
		{
		IP2366DCDCState=IP2366DCState_LowTemp;
		IsSystemLowTemp=true;
		ShowPostInfo(78,"电池温度过低\0","WF",Msg_Warning);
		delay_Second(1);
		ShowPostInfo(78,"已禁止电池充电\0","WF",Msg_Warning);
		delay_Second(1);
		}
		
	//设置芯片睡眠功能
	if(!IP2366_SetDeepSleepModeEnabled(CfgData.SleepCfg==System_Sleep_Deep?true:false))
		{
		ShowPostInfo(78,"设置系统模式失败\0","F1",Msg_Fault);
		SelfTestErrorHandler();
		}
	else if(CfgData.SleepCfg!=System_Sleep_Deep)
		{
		ShowPostInfo(78,"即插即用模式已开启\0","29",Msg_INFO);
		delay_ms(400);
		ShowPostInfo(78,"待机功耗将增大\0","29",Msg_INFO);
		delay_ms(400);
		}
	//再次检测固件版本
	ShowPostInfo(79,"二次读取芯片版本\0","2A",Msg_Statu);
  if(!IP2366_GetFirmwareTimeStamp(VendorString))		
		{
		ShowPostInfo(79,"读取芯片版本失败\0","E6",Msg_Fault);
		SelfTestErrorHandler();
		}		
	if(strncmp(CurrentIP2366FW->FWID,VendorString,5))	
		{
		ShowPostInfo(79,"芯片版本数据错误\0","FB",Msg_Fault);
		SelfTestErrorHandler();		
		}
	//判断是否支持超充以及是否开启超充
	if(CfgData.MaxVPD==PDMaxIN_28V)Result=true;
	else if(CfgData.InputConfig.ChargeCurrent>CurrentIP2366FW->IP2366ICCMAX)Result=true;
	else if(CfgData.InputConfig.ChargePower>CurrentIP2366FW->MaxCapableChgPower)Result=true;
	else Result=false;
	if(CurrentIP2366FW->IsHyperChargeCapable)
		{
		ShowPostInfo(79,"超充模式已启用\0","2B",Msg_Statu);
		if(CfgData.IStop==IStop_100mA||CfgData.IStop==IStop_150mA)
			{
			ShowPostInfo(79,"停充电流非法\0","W9",Msg_Warning);
			delay_Second(1);
			ShowPostInfo(79,"已自动修正\0","W9",Msg_Warning);
			delay_Second(1);
			CfgData.IStop=IStop_200mA;
			TryToSaveConfigDuringPost(79);
			}
		if(EnableDetailOutput)delay_ms(300);
		}
   else if(Result)
		{
		ShowPostInfo(79,"芯片为公版固件\0","2C",Msg_Warning);
		delay_Second(1);
		ShowPostInfo(79,"超充模式已禁用\0","2C",Msg_Warning);
		delay_Second(1);
		//将峰值限流调回去
		CfgData.MaxVPD=PDMaxIN_20V;
		CfgData.InputConfig.ChargeCurrent=CurrentIP2366FW->IP2366ICCMAX;
		CfgData.InputConfig.ChargePower=CurrentIP2366FW->MaxCapableChgPower;
		TryToSaveConfigDuringPost(79);
		}
	//检查50mA per LSB的PDO支持
	if(!CurrentIP2366FW->IsExtendPDOCapable&&CfgData.FixedPDOCfg.PDO20VICCMAX>4000)
		{
		ShowPostInfo(79,"芯片为公版固件\0","2D",Msg_Warning);
		delay_Second(1);
		ShowPostInfo(79,"20V高功率已禁用\0","2D",Msg_Warning);
		delay_Second(1);
		//关闭20V PDO的4A以上设置
		CfgData.FixedPDOCfg.PDO20VICCMAX=4000;
		CfgData.FixedPDOCfg.IsEnable20VPDOSet=false;
		TryToSaveConfigDuringPost(79);
		}
	//检查
	else if(!CurrentIP2366FW->IsExtendPDOCapable&&(CfgData.FixedPDOCfg.PDO20VICCMAX%50))
		{
		ShowPostInfo(79,"20V PDO电流值非法\0","WA",Msg_Warning);
		delay_Second(1);
		ShowPostInfo(79,"已自动修正\0","WA",Msg_Warning);
		delay_Second(1);
		//修正PDO结果
		i=CfgData.FixedPDOCfg.PDO20VICCMAX/50;
		i*=50;
	  if(i>7000)i=7000;
		if(i<1000)i=1000;
		CfgData.FixedPDOCfg.PDO20VICCMAX=i;
		TryToSaveConfigDuringPost(79);		
		}
	//检查高压SCP支持	
	if(!!CurrentIP2366FW->IsHSCPCapable&&CfgData.OutputConfig.IsEnableHSCPOut)
		{
		ShowPostInfo(78,"芯片为公版固件\0","2E",Msg_Warning);
		delay_Second(1);
		ShowPostInfo(78,"高功率SCP已禁用\0","2E",Msg_Warning);
		delay_Second(1);
		//关闭高功率SCP功能
		CfgData.OutputConfig.IsEnableHSCPOut=false;
		TryToSaveConfigDuringPost(79);	
		}
	//设置再充电参数
	ShowPostInfo(80,"设置再充电参数\0","2F",Msg_Statu);	
	if(!IP2366_SetReChargeParam(CfgData.VRecharge,CfgData.IStop))
		{
		ShowPostInfo(80,"再充参数设置失败\0","F2",Msg_Fault);
		SelfTestErrorHandler();
		}
	//设置低压保护参数
	ShowPostInfo(82,"设置低压保护电压\0","30",Msg_Statu);	
	if(!IP2366_SetVLowVolt(CfgData.Vlow))	
		{
		ShowPostInfo(82,"低压保护设置失败\0","F3",Msg_Fault);
		SelfTestErrorHandler();
		}
	//开始写寄存器
	CurrentStorDisState=IP2366_IsEnableDischarge(ADCO.Vbatt);	
	if(!IsBootFromVBUS)
		{
		ShowPostInfo(85,"设置放电系统\0","31",Msg_Statu);	
		if(!IP2366_InitOutputSystem(CurrentStorDisState))
			{
			ShowPostInfo(85,"放电系统设置失败\0","F4",Msg_Fault);
			SelfTestErrorHandler();
			}
		}
	//设置输入
	ShowPostInfo(88,"设置充电系统\0","32",Msg_Statu);
	switch(StorageMode)
		{
		//根据存储模式配置输出
		case StorageMode_OFF:ICFG.FullVoltage=CfgData.InputConfig.FullVoltage;break; //存储模式禁用,使用系统设置的最高电压
		case StorageMode_3V6:ICFG.FullVoltage=3600;break; //存储模式启用，电池最大电压3.6V
		case StorageMode_3V7:ICFG.FullVoltage=3700;break; //存储模式启用，电池最大电压3.7V
	  case StorageMode_3V8:ICFG.FullVoltage=3800;break;	//存储模式启用，电池最大电压3.8V
		}
	ICFG.ChargePower=CfgData.InputConfig.ChargePower;	
	ICFG.PreChargeCurrent=CfgData.InputConfig.PreChargeCurrent; //其他参数照常填写
	ICFG.IsEnableCharger=IsSystemLowTemp?false:true; 						//充电器如果是低温保护，则关闭
	ICFG.ChargeCurrent=DCDCOutputBit?CurrentIP2366FW->IP2366ICCMAX:CfgData.InputConfig.ChargeCurrent; //初始化时如果开启输出则填写9.7A	
  //写寄存器设置充电系统配置
	Result=IP2366_SetSinkProtocol(&CfgData.SinkConfig);
	Result&=UpdateSinkPower(true);
	Result&=IP2366_SetInputState(&ICFG,true);
	if(!Result)
		{
		//出错了，提示设置失败
		ShowPostInfo(88,"充电系统设置失败\0","F5",Msg_Fault);
		SelfTestErrorHandler();	
		}
	//设置PDO参数
	ShowPostInfo(92,"设置PDO广播\0","33",Msg_Statu);
	IsCmdSendOK=IP2366_SetFixedPDO(&CfgData.FixedPDOCfg); //设置固定挡位的PDO参数
	if(!IsCmdSendOK||!IP2366_SetPDOBroadCast(&CfgData.PDOCFG))
		{
		if(!IsCmdSendOK)ShowPostInfo(92,"PDO电流设置失败\0","F7",Msg_Fault);
		else ShowPostInfo(92,"PDO广播设置失败\0","F6",Msg_Fault);
		SelfTestErrorHandler();		
		}
	//设置PPS配置
	ShowPostInfo(93,"设置PPS广播\0","34",Msg_Statu);
	if((CfgData.PPSConfig.PPS1Current>3000||CfgData.PPSConfig.PPS2Current>3000)&&!CurrentIP2366FW->IsExtendPDOCapable)	
		{
		ShowPostInfo(93,"芯片为公版固件\0","35",Msg_Warning);
		delay_Second(1);
		ShowPostInfo(93,"PPS电流已重置\0","35",Msg_Warning);
		delay_Second(1);
		//重置PPS电流为芯片默认值
		CfgData.PPSConfig.PPS1Current=3000;
		CfgData.PPSConfig.PPS2Current=3000;
		CfgData.PPSConfig.IsEnablePPS1Set=false;
		CfgData.PPSConfig.IsEnablePPS2Set=false;
		TryToSaveConfigDuringPost(93);		
		}		
	//写入寄存器设置PPS
	if(!IP2366_SetPPSCurrent(&CfgData.PPSConfig))
		{
		ShowPostInfo(93,"PPS广播设置失败\0","F8",Msg_Fault);
		SelfTestErrorHandler();		
		}	
	//发送重新握手的指令
	ShowPostInfo(94,"发送TypeC重连命令\0","36",Msg_Statu);
	
  if(!IsBootFromVBUS)do
		{
		IsCmdSendOK=IP2366_SetTypeCRole(TypeC_NoConnect);
		delay_ms(200);
		//根据系统配置，计算C口模式
		if(CfgData.StorageModeINROM!=StorageMode_OFF)
			{
			//存储模式下只有电池电压高于允许值才启用对外输出模式,否则配置为仅充电
			VdroopRate=(ADCO.Vbatt/(float)BattCellCount)*(float)1000;
			i=(int)VdroopRate;																					//将测量到的电池电压转换为单节电池的等效电压并换算为mV
			Result=i>ICFG.FullVoltage?true:false;
			} 
		else if(CfgData.OutputConfig.IsEnableOutput)Result=true;  //非存储模式下如果系统开启输出，则配置为DRP
		else Result=false;
		//设置C口状态
		IsCmdSendOK&=IP2366_SetTypeCRole(Result?TypeC_Bidir:TypeC_SinkOnly);
		delay_ms(200);
		IsCmdSendOK&=IP2366_SetOTPSign();
		if(IsCmdSendOK)break;
		retry--;
		ShowPostInfo(94,"重连命令重试中\0","37",Msg_Warning);
		}
	while(retry>0);
	//否则只执行设置OTP
	else do
		{
		AUXPSU_SetIPDState(true); //重新打开输入下拉，使能充电器
		IsCmdSendOK=IP2366_SetOTPSign();
		if(IsCmdSendOK)break;
		retry--;
		delay_ms(10);
		ShowPostInfo(94,"重连命令重试中\0","37",Msg_Warning);
		}
	while(retry>0);
	//尝试失败
	if(!retry)
		{
		ShowPostInfo(94,"重连命令发送失败\0","F9",Msg_Fault);
		SelfTestErrorHandler();
		}
	IP2366_ClearOCFlag(); //移除OC Flag		
	//后处理完毕，此时如果是从VBUS启动的，则复位定时器
	if(IsBootFromVBUS)WaitAfterTypeCRemoved=50;	
	}
