redstoner-35/DFEx-FarBeaMon3tr/固件/电池棒控制器固件/User/inc/pic.h

#ifndef __PIC_H
#define __PIC_H

//AIMPACT Logo
const unsigned char PostSign[2002] = {
0X00,0X00,0X00,0X00,0X00,0X00,0X00,0X00,0X00,0X00,0X00,0X00,0X00,0X00,0X00,0X00,
0X00,0X00,0X00,0X00,0X00,0X00,0X00,0X00,0X00,0X00,0X00,0X00,0X00,0X00,0X00,0X00,
0X00,0X00,0X00,0X00,0X00,0X00,0X00,0X00,0X00,0X00,0X00,0X00,0X00,0X00,0XFD,0X79,
0XFD,0X79,0X00,0X00,0X00,0X00,0X00,0X00,0X00,0X00,0X00,0X00,0X00,0X00,0X00,0X00,
0X00,0X00,0XFD,0X79,0XFD,0X79,0X00,0X00,0X00,0X00,0X00,0X00,0X00,0X00,0X00,0X00,
0X25,0X89,0X25,0X89,0X25,0X89,0X25,0X89,0X25,0X89,0X25,0X89,0X25,0X89,0X00,0X00,
0X00,0X00,0X00,0X00,0X00,0X00,0X00,0X00,0X00,0X00,0X00,0X00,0X00,0X00,0X00,0X00,
0X00,0X00,0X00,0X00,0X00,0X00,0X00,0X00,0X00,0X00,0X00,0X00,0X00,0X00,0X00,0X00,
0X00,0X00,0X00,0X00,0X00,0X00,0X00,0X00,0X00,0X00,0XA2,0X54,0XA2,0X54,0XA2,0X54,
0XA2,0X54,0XA2,0X54,0XA2,0X54,0XA2,0X54,0X00,0X00,0X00,0X00,0X00,0X00,0X00,0X00,
0X3A,0X59,0X3A,0X59,0X3A,0X59,0X3A,0X59,0X3A,0X59,0X3A,0X59,0X3A,0X59,0X3A,0X59,
0X3A,0X59,0X3A,0X59,0X00,0X00,0X00,0X00,0X00,0X00,0X00,0X00,0X00,0X00,0X00,0X00,
0XFF,0X80,0XFF,0X80,0X00,0X00,0X00,0X00,0X00,0X00,0X00,0X00,0X00,0X00,0X00,0X00,
0X00,0X00,0X00,0X00,0X00,0X00,0X00,0X00,0XE8,0XE4,0X00,0X00,0X00,0X00,0X00,0X00,
0X00,0X00,0X00,0X00,0XFD,0X79,0XFD,0X79,0XFD,0X79,0X00,0X00,0X00,0X00,0X00,0X00,
0X00,0X00,0X00,0X00,0X00,0X00,0XFD,0X79,0XFD,0X79,0XFD,0X79,0X00,0X00,0X00,0X00,
0X00,0X00,0X00,0X00,0X00,0X00,0X25,0X89,0X25,0X89,0X25,0X89,0X25,0X89,0X25,0X89,
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
0X41,0XFE,0X41,0XFE,0X41,0XFE,0X41,0XFE,0X41,0XFE,0X41,0XFE,0X41,0XFE,0X41,0XFE,
0X41,0XFE,0X41,0XFE,0X41,0XFE,0X41,0XFE,0X41,0XFE,0X41,0XFE,0X41,0XFE,0X41,0XFE,
0X41,0XFE,0X41,0XFE,0X41,0XFE,0X41,0XFE,0X41,0XFE,0X41,0XFE,0X41,0XFE,0X41,0XFE,
};

#endif
