redstoner-35/DFEx-FarBeaMon3tr/固件/电池棒控制器固件/User/ht32f5xxxx_01_it.c

/*********************************************************************************************************//**
 * @file    GPIO/InputOutput/ht32f5xxxx_01_it.c
 * @version $Rev:: 2970         $
 * @date    $Date:: 2018-08-03#$
 * @brief   This file provides all interrupt service routine.
 *************************************************************************************************************
 * @attention
 *
 * Firmware Disclaimer Information
 *
 * 1. The customer hereby acknowledges and agrees that the program technical documentation, including the
 *    code, which is supplied by Holtek Semiconductor Inc., (hereinafter referred to as "HOLTEK") is the
 *    proprietary and confidential intellectual property of HOLTEK, and is protected by copyright law and
 *    other intellectual property laws.
 *
 * 2. The customer hereby acknowledges and agrees that the program technical documentation, including the
 *    code, is confidential information belonging to HOLTEK, and must not be disclosed to any third parties
 *    other than HOLTEK and the customer.
 *
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
 * <h2><center>Copyright (C) Holtek Semiconductor Inc. All rights reserved</center></h2>
 ************************************************************************************************************/

/* Includes ------------------------------------------------------------------------------------------------*/
#include "ht32.h"
#include "Key.h"
#include "LCD_Init.h"

/** @addtogroup HT32_Series_Peripheral_Examples HT32 Peripheral Examples
  * @{
  */

/** @addtogroup GPIO_Examples GPIO
  * @{
  */

/** @addtogroup InputOutput
  * @{
  */
/* Defines ------------------------------------------------------------------------------------------------*/


/* Global functions ----------------------------------------------------------------------------------------*/
/*********************************************************************************************************//**
 * @brief   This function handles NMI exception.
 * @retval  None
 ************************************************************************************************************/
void NMI_Handler(void)
{
}

/*********************************************************************************************************//**
 * @brief   This function handles Hard Fault exception.
 * @retval  None
 ************************************************************************************************************/
void HardFault_Handler(void)
{
  #ifdef EnableDebugMode	 

  static vu32 gIsContinue = 0;
  /*--------------------------------------------------------------------------------------------------------*/
  /* For development FW, MCU run into the while loop when the hardfault occurred.                           */
  /* 1. Stack Checking                                                                                      */
  /*    When a hard fault exception occurs, MCU push following register into the stack (main or process     */
  /*    stack). Confirm R13(SP) value in the Register Window and typing it to the Memory Windows, you can   */
  /*    check following register, especially the PC value (indicate the last instruction before hard fault).*/
  /*    SP + 0x00    0x04    0x08    0x0C    0x10    0x14    0x18    0x1C                                   */
  /*           R0      R1      R2      R3     R12      LR      PC    xPSR                                   */
  while (gIsContinue == 0)
  {
  }
  /* 2. Step Out to Find the Clue                                                                           */
  /*    Change the variable "gIsContinue" to any other value than zero in a Local or Watch Window, then     */
  /*    step out the HardFault_Handler to reach the first instruction after the instruction which caused    */
  /*    the hard fault.                                                                                     */
  /*--------------------------------------------------------------------------------------------------------*/

  #else
  NVIC_SystemReset();
  #endif
}

/*********************************************************************************************************//**
 * @brief   This function handles SVCall exception.
 * @retval  None
 ************************************************************************************************************/
void SVC_Handler(void)
{
}

/*********************************************************************************************************//**
 * @brief   This function handles PendSVC exception.
 * @retval  None
 ************************************************************************************************************/
void PendSV_Handler(void)
{
}
/*********************************************************************************************************//**
 * @brief   This function handles SysTick Handler.
 * @retval  None
 ************************************************************************************************************/
extern char DelaySeconds;

void SysTick_Handler(void)
{
	//秒数倒计时
  if(DelaySeconds)DelaySeconds--;
}
/*********************************************************************************************************//**
 * @brief   This function handles EXTI 4~15 interrupt.
 * @retval  None
 ************************************************************************************************************/
void EXTI4_15_IRQHandler(void)
{
 //EXTI4-15属于按键，进行侧按处理
 SideKey_IntCallback();
}

/*********************************************************************************************************//**
 * @brief   This function handles ADC interrupt.
 * @retval  None
 ************************************************************************************************************/
void ADC_EOC_interrupt_Callback(void);

void ADC_IRQHandler(void)
{
  if(ADC_GetIntStatus(HT_ADC0, ADC_INT_CYCLE_EOC) == SET)
    ADC_EOC_interrupt_Callback();//进行中断处理
}
/*********************************************************************************************************//**
 * @brief   This function handles PDMA-CH0-1 interrupt.
 * @retval  None
 ************************************************************************************************************/
void PDMA_CH0_1_IRQHandler(void)
 {
 //LCD TX有效
 if(PDMA_GetFlagStatus(PDMA_SPI0_TX,PDMA_FLAG_TC))
  {
	PDMA_ClearFlag(PDMA_SPI0_TX,PDMA_FLAG_TC);//清除flag
	IsPDMATranferDone=true;
	}
}

/*********************************************************************************************************//**
 * @brief   This function handles GPTM0 interrupt.
 * @retval  None
 ************************************************************************************************************/
extern bool SensorRefreshFlag;

void GPTM0_IRQHandler(void)
 {
   //更新事件标志位使能
	 if(TM_GetFlagStatus(HT_GPTM0,TM_INT_UEV))
	  {
		TM_ClearFlag(HT_GPTM0,TM_INT_UEV);
		SensorRefreshFlag=true;//请求传感器刷新
		}
 }
