redstoner-35/DFEx-FarBeaMon3tr/固件/电池棒控制器固件/Hardware/PMSetup.c

#include "ht32.h"
#include "delay.h"
#include "Pindefs.h"
#include "GUI.h"
#include "Config.h"
#include "IP2366_REG.h"
#include "INA226.h"
#include "PCA9536.h"
#include "LCD_Init.h"
#include "BalanceMgmt.h"
#include "AUXPSU.h"
#include "LogSystem.h"

//电源管理引脚自动定义
#define LDO_EN_IOB STRCAT2(GPIO_P,LDO_EN_IOBank)
#define LDO_EN_IOG STRCAT2(HT_GPIO,LDO_EN_IOBank)
#define LDO_EN_IOP STRCAT2(GPIO_PIN_,LDO_EN_IOPinNum) 

//int引脚自动定义
#define IP2366_INT_IOB STRCAT2(GPIO_P,IP2366_INT_IOBank)
#define IP2366_INT_IOG STRCAT2(HT_GPIO,IP2366_INT_IOBank)
#define IP2366_INT_IOP STRCAT2(GPIO_PIN_,IP2366_INT_IOPinNum) 

//EN引脚自动定义
#define IP2366_EN_IOB STRCAT2(GPIO_P,IP2366_EN_IOBank)
#define IP2366_EN_IOG STRCAT2(HT_GPIO,IP2366_EN_IOBank)
#define IP2366_EN_IOP STRCAT2(GPIO_PIN_,IP2366_EN_IOPinNum) 

//内部变量
short SleepTimer; //睡眠定时 
short IPStallTime=0; //IP2368重启

//初始化IO完成自举操作
void PowerMgmtSetup(void)
  {
	 //配置GPIO
   AFIO_GPxConfig(LDO_EN_IOB,LDO_EN_IOP, AFIO_FUN_GPIO);
   GPIO_DirectionConfig(LDO_EN_IOG,LDO_EN_IOP,GPIO_DIR_OUT);//配置为输出 
	 GPIO_DriveConfig(LDO_EN_IOG,LDO_EN_IOP,GPIO_DV_16MA);	//设置为16mA最大输出	
	 GPIO_ClearOutBits(LDO_EN_IOG,LDO_EN_IOP);//默认输出设置为0
	 
	 AFIO_GPxConfig(IP2366_INT_IOB,IP2366_INT_IOP, AFIO_FUN_GPIO);
	 GPIO_DirectionConfig(IP2366_INT_IOG,IP2366_INT_IOP,GPIO_DIR_IN);//设置为高阻输入
	 GPIO_InputConfig(IP2366_INT_IOG,IP2366_INT_IOP,ENABLE);  //打开输入寄存器
	 GPIO_PullResistorConfig(IP2366_INT_IOG,IP2366_INT_IOP,GPIO_PR_DOWN); //打开下拉
		
   AFIO_GPxConfig(IP2366_EN_IOB,IP2366_EN_IOP, AFIO_FUN_GPIO);
   GPIO_DirectionConfig(IP2366_EN_IOG,IP2366_EN_IOP,GPIO_DIR_OUT);//配置为输出 
	 GPIO_DriveConfig(IP2366_EN_IOG,IP2366_EN_IOP,GPIO_DV_16MA);	//设置为16mA最大输出			
	 //设置输出
   GPIO_ClearOutBits(IP2366_EN_IOG,IP2366_EN_IOP); //2366-EN=0
	 delay_ms(100);
	 GPIO_SetOutBits(LDO_EN_IOG,LDO_EN_IOP);//输出设置为1
	 //配置自动休眠计时器
	 SleepTimer=960; //2分钟无操作自动休眠
	}
	
//Type-C连接失败时，进行重新握手的部分
void IP2366StallRestore(void)
  {
	int wait;
	//计时累加部分
	IPStallTime++;
	if(IPStallTime>=32) //IP2366掉线大约4秒后开始重试
	  {
		IPStallTime=0;  //操作复位，等待下次计时
		//设置为高阻输入使2366休眠
		GPIO_InputConfig(IP2366_INT_IOG,IP2366_INT_IOP,ENABLE); 
	  GPIO_DirectionConfig(IP2366_INT_IOG,IP2366_INT_IOP,GPIO_DIR_IN);
		//给EN发送脉冲
		delay_ms(200);	
		GPIO_SetOutBits(IP2366_EN_IOG,IP2366_EN_IOP); 
	  delay_ms(200);
    GPIO_ClearOutBits(IP2366_EN_IOG,IP2366_EN_IOP);	//令2366-EN=1，尝试监测		
		//监测是否成功唤醒
		wait=300; //唤醒检测延时300mS
		do
		  {
			wait--;
      if(wait<=0)break;	//200mS后IP2368唤醒失败，退出
			delay_ms(1);		
			}
		while(GPIO_ReadInBit(IP2366_INT_IOG,IP2366_INT_IOP)==SET); //IP2366位于唤醒状态，等待唤醒结束
		//如果成功，则再100mS后锁住INT使2366保持唤醒
		if(wait>0)delay_ms(100);
		GPIO_InputConfig(IP2366_INT_IOG,IP2366_INT_IOP,DISABLE); 
	  GPIO_DirectionConfig(IP2366_INT_IOG,IP2366_INT_IOP,GPIO_DIR_OUT);//禁用IDR，设置为输出
	  GPIO_SetOutBits(IP2366_INT_IOG,IP2366_INT_IOP); //令INT保持在1,使IP2366永远唤醒不得睡眠	
    }
	}		
	
//强制2366断电
void Force2366ToRestart(void)
	{
	//设置为高阻输入使2366休眠
	GPIO_InputConfig(IP2366_INT_IOG,IP2366_INT_IOP,ENABLE); 
	GPIO_DirectionConfig(IP2366_INT_IOG,IP2366_INT_IOP,GPIO_DIR_IN);
	IP2366_SetDeepSleepModeEnabled(true);
	IP2366_ForceEnterDeepSleep(); //给IP2366强制放发送指令
	}
	
//强制关机
void ShutSysOFF(void)
	{
	extern bool IsEnablePowerOFF;
	if(!IsEnablePowerOFF)return; //不允许关机
	//复位LCD
	DoThingsBeforeOFF(); //执行退出构造函数
	ClearScreen();
	LCD_DeInit(); //除能LCD
	Balance_ForceDiasble(); //发送命令关闭均衡系统
	//如果是非完全睡眠模式则进行对应的处理
	if(CfgData.SleepCfg!=System_Sleep_Deep)
		{
		AUXPSU_ConnectTCtoIP2366(); //将Type-C的CC连接到IP2366
		AUXPSU_SwitchToPassThrough(); //切换到直通模式
		INA226_EnterPowerDownMode();
		LCD_DisableBlackLight(); //关闭LCD背光开始休眠	
		}	
	//完全睡眠模式，根据系统是否处于安全模式进行切换继电器
	else 
		{
		AUXPSU_SetIPDState(true);
		if(!IsBootFromVBUS)AUXPSU_ConnectTCtoIP2366();		//系统关机前不在安全模式，令继电器将CC切换到2366
		else AUXPSU_ConnectTCtoIPD();                     //系统关机前位于安全模式，切换到内置下拉
		IP2366_ForceEnterDeepSleep(); 										//给IP2366发送强制睡眠指令
		}
	//使系统掉电
	GPIO_ClearOutBits(LDO_EN_IOG,LDO_EN_IOP);//输出设置为0,关闭LDO电源强迫单片机掉电
	delay_ms(300);
	NVIC_SystemReset();
	while(1);		
	}	
	
//给2366踢一脚把2366踹醒
void KickIP2366ToWakeUp(void)
	{
	int retry=3;
	char WakeMsg[]={"唤醒重试次数:3"};
	ShowPostInfo(12,"唤醒充电IC","05",Msg_Statu);
	//如果INT=0说明2366在睡觉
	if(GPIO_ReadInBit(IP2366_INT_IOG,IP2366_INT_IOP)==RESET)do
		{
		
		GPIO_SetOutBits(IP2366_EN_IOG,IP2366_EN_IOP); //令2366-EN=1
		delay_ms(50);
		GPIO_DirectionConfig(IP2366_INT_IOG,IP2366_INT_IOP,GPIO_DIR_OUT);
		GPIO_SetOutBits(IP2366_INT_IOG,IP2366_INT_IOP); 									//同时设置IP2366的INT为1尝试踢醒在非深度睡眠状态的2366
	  delay_ms(200);
    GPIO_ClearOutBits(IP2366_EN_IOG,IP2366_EN_IOP);										//令2366-EN=0，发出一个短脉冲模拟EN按键按下
		GPIO_DirectionConfig(IP2366_INT_IOG,IP2366_INT_IOP,GPIO_DIR_IN);
		GPIO_ClearOutBits(IP2366_INT_IOG,IP2366_INT_IOP);                  //令INT=0释放2366 INT然后准备检测是否唤醒成功
		delay_ms(200);		
		if(GPIO_ReadInBit(IP2366_INT_IOG,IP2366_INT_IOP)==SET)break; //唤醒成功
		//尝试失败，提示唤醒剩余次数
		retry--;
		WakeMsg[13]=0x30+(3-retry);
		ShowPostInfo(12,WakeMsg,"W1",Msg_Warning);		
    //延时2秒后重试			
    delay_Second(2);	
		}	
	while(retry); 
	//唤醒失败
	if(!retry)
		{
		ShowPostInfo(12,"充电IC唤醒失败","E4",Msg_Fault);
		SelfTestErrorHandler();
		}
	GPIO_SetOutBits(IP2366_INT_IOG,IP2366_INT_IOP);
	GPIO_DirectionConfig(IP2366_INT_IOG,IP2366_INT_IOP,GPIO_DIR_OUT);
	GPIO_InputConfig(IP2366_INT_IOG,IP2366_INT_IOP,DISABLE);  //设置为推挽输出保持2366唤醒
	}

//休眠状态判断
void IP2366_ReInitBasedOnConfig(void);
void IP2366_SetIBatLIMBaseOnSysCfg(void);
	
void PowermanagementSleepControl(void)
  {
	extern bool IsEnablePowerOFF;
	extern bool IsConfigSaved;
	extern int BalanceForceEnableTIM;
	//当前未处于睡眠状态、均衡开启或者Type-C处于连接中，不执行
	if(!IsEnablePowerOFF||BalanceForceEnableTIM)
		{
		SleepTimer=960;	
		return; //复位计时器
		}
	if(SleepTimer<8)Balance_ForceDiasble(); //强制关闭均衡器	
	//时间未到继续计时
	if(SleepTimer>0)return;
	DoThingsBeforeOFF(); //执行退出构造函数
	//掉电之前先进行存盘和重配置芯片处理（如果打开睡眠模式的话需要重配置否则芯片睡不醒）
  if(IsConfigSaved||!CheckIfConfigIsSame())
		{
		IP2366_ReInitBasedOnConfig(); //设置芯片配置
		IP2366_SetIBatLIMBaseOnSysCfg(); //设置动态限流
		IsConfigSaved=false;
		}	
	if(CfgData.AutoSaveCfg==AutoSave_Enabled||!CfgData.EnableAdvAccess)WriteConfiguration(&CfgUnion,false); //开启自动存盘(非管理员模式)在断电前进行存盘
	//非完全掉电睡眠模式，系统关闭INA226和PCA9536降低VCCIO功耗，令系统进入睡眠
	if(CfgData.SleepCfg!=System_Sleep_Deep)
		{
		AUXPSU_ConnectTCtoIP2366(); //将Type-C的CC连接到IP2366确保可以瞬间唤醒
		INA226_EnterPowerDownMode();
		ClearScreen();
		AUXPSU_SwitchToPassThrough(); //切换到直通模式
		LCD_DisableBlackLight(); //关闭LCD背光开始休眠
		//令IP2366进入睡眠后使系统掉电
		GPIO_InputConfig(IP2366_INT_IOG,IP2366_INT_IOP,ENABLE); 
		GPIO_DirectionConfig(IP2366_INT_IOG,IP2366_INT_IOP,GPIO_DIR_IN);//设置为高阻输入使2366休眠		
		IP2366_ForceEnterDeepSleep(); //给IP2366强制放发送指令
		GPIO_ClearOutBits(LDO_EN_IOG,LDO_EN_IOP);//输出设置为0,关闭LDO电源强迫单片机掉电
		while(1);		
		}
	//完全睡眠模式，根据系统是否处于安全模式进行切换继电器
	else 
		{
		AUXPSU_SetIPDState(true);
		if(!IsBootFromVBUS)AUXPSU_ConnectTCtoIP2366();		//系统关机前不在安全模式，令继电器将CC切换到2366
		else AUXPSU_ConnectTCtoIPD();                     //系统关机前位于安全模式，切换到内置下拉
		}
	//所有操作完毕，开始检测
	GPIO_InputConfig(IP2366_INT_IOG,IP2366_INT_IOP,ENABLE); 
	GPIO_DirectionConfig(IP2366_INT_IOG,IP2366_INT_IOP,GPIO_DIR_IN);//设置为高阻输入使2366休眠	
	if(GPIO_ReadInBit(IP2366_INT_IOG,IP2366_INT_IOP)==SET)
		{
		SleepTimer=4;
		IP2366_ForceEnterDeepSleep(); //给IP2366强制放发送指令
		return; //如果IP2366未进入睡眠则继续等待
		}
	//立即释放IO
	ClearScreen();
	GPIO_ClearOutBits(LDO_EN_IOG,LDO_EN_IOP);//输出设置为0,关闭LDO电源强迫单片机掉电
	while(1);		
	}
