redstoner-35/DFEx-FarBeaMon3tr/固件/电池棒控制器固件/User/inc/IP2366_REG.h

#ifndef _2366REG_
#define _2366REG_

#include <stdbool.h>

typedef enum
	{
	//可读写寄存器
	REG_SYSCTL0=0,
	REG_SYSCTL2=2,
	REG_SYSCTL3=3,
	REG_SYSCTL6=6,
	REG_SYSCTL8=8,
	REG_SYSCTL9=9,
	REG_SYSCTL10=0x0A,
	REG_SYSCTL11=0x0B,
	REG_SYSCTL12=0x0C,
	REG_SELECT_PDO=0x0D,
	REG_TYPEC_CTL8=0x22,
	REG_TYPEC_CTL9=0x23,
	REG_TYPEC_CTL10=0x24,
	REG_TYPEC_CTL11=0x25,
	REG_TYPEC_CTL12=0x26,
	REG_TYPEC_CTL13=0x27,
	REG_TYPEC_CTL14=0x28,	
	REG_TYPEC_CTL17=0x2B,
	REG_TYPEC_CTL18=0x2C,
	REG_TYPEC_CTL23=0x29,
	REG_TYPEC_CTL24=0x2A,
  //只读寄存器
	REG_STATE_CTL0=0x31,
  REG_STATE_CTL1=0x32,
	REG_STATE_CTL2=0x33,
	REG_STATE_CTL3=0x38,
  REG_TYPEC_STATE=0x34,
	REG_RECEIVED_PDO=0x35,
	REG_MFR_ICREV=0x39,
  REG_IC_TEMP=0x3A,
	REG_VBAT_LSB=0x50,
	REG_VBAT_MSB=0x51,
  REG_VSYS_LSB=0X52,
	REG_VSYS_MSB=0X53,
	REG_IBAT_LSB=0X6E,
	REG_IBAT_MSB=0X6F,
	REG_ISYS_LSB=0X70,
	REG_ISYS_MSB=0X71,
	REG_PSYS_LSB=0x74,
	REG_PSYS_MSB=0x75
	}IP2366REGDef;

typedef enum
	{
	Power_30W=0,
	Power_45W=1,
	Power_60W=2,
	Power_65W=3,
	Power_100W=4,
	Power_140W=5
	}ChargePowerDef;

typedef enum
	{
	IStop_50mA=1,
	IStop_100mA=2,
	IStop_150mA=3,
	IStop_200mA=4,
	IStop_250mA=5,
	IStop_300mA=6,
	IStop_350mA=7,
	IStop_400mA=8,
	IStop_450mA=9,
	IStop_500mA=10
	}IStopConfig;	 //停充电流设置
	
typedef enum
	{
	Recharge_Disable=0, //关闭再充电
	Recharge_0V05=1, //电池电压低于浮充0.05V时再充电
	Recharge_0V1=2, //电池电压低于浮充0.1V时再充电
	Recharge_0V2=3 //电池电压低于浮充0.2V时再充电
	}ReChargeConfig; //再充电配置
	
	
typedef enum
 {
 QuickCharge_PD,
 QuickCharge_HV, //其余高压快充
 QuickCharge_HC, //低电压高电流快充
 QuickCharge_None, //无快充
 QuickCharge_PlaceHolder, //QC枚举里面的占位符，其实没用只是用来复位GUI
 }QuickChargeStateDef;	
 
typedef enum
{
Hardware_Ver_Unknown=0, //未知版本或者没有该寄存器
Hardware_Ver_B=1,
Hardware_Ver_C=2,
Hardware_Ver_D=3,       //对应芯片硬件版本BCD
}IP2366HWRevDef;
 
typedef enum
 {
 Batt_StandBy,
 Batt_PreChage,
 Batt_CCCharge,
 Batt_CVCharge,
 Batt_ChgWait,
 Batt_ChgDone,
 Batt_ChgError,
 Batt_discharging,
 }BatteryStateDef;	
 
typedef enum
	{
	RecvPDO_None, //没有PDO
	RecvPDO_5V, //收到5V
	RecvPDO_9V, //9V
	RecvPDO_12V, //12V
	RecvPDO_15V, //15V
	RecvPDO_20V, //20V
	}RecvPDODef;	
 
typedef struct
	{
	bool PDO5VOK;
	bool PDO9VOK;
	bool PDO12VOK;
	bool PDO15VOK;
	bool PDO20VOK;	
	}RecvPDOListDef;	
	
typedef struct
	{
	bool EnablePPS2;
	bool EnablePPS1;
	bool Enable20V;
	bool Enable15V;
	bool Enable12V;
	bool Enable9V;
	}PDOBroadcastDef;	
	
typedef enum
 {
 PD_5VMode=1,
 PD_7VMode=2,
 PD_9VMode=3,
 PD_12VMode=4,
 PD_15VMode=5,
 PD_20VMode=6,
 PD_28VMode=7
 }PDStateDef;	
	
typedef struct
	{
	bool IsEnableCharger; //是否开启充电
	int ChargeCurrent; //恒流充电电流设置(mA)
	int PreChargeCurrent; //涓流充电电流设置(mA)
	int FullVoltage; //电池满电电压
	ChargePowerDef ChargePower; //最大输出功率
	}IP2366InputDef;	
	
typedef enum
	{
	VSys_State_Normal,
	VSys_State_OCP,
	VSys_State_Short
	}VSysStateDef;	
	
typedef enum
	{
	VBUS_NoPower,
	VBUS_Normal,
	VBUS_OverVolt,
	}VbusVoltStateDef;	
	
typedef struct
	{
	VbusVoltStateDef VBusState;
	VSysStateDef VSysState;
	}ChipStatDef;	
	
typedef struct
	{
	bool EnableSinkDPDM; 		//是否让IC尝试握手USB2.0DP DM协商的老协议(如SCP QC等)对电池进行充电
	bool EnableSinkPD;   		//是否让IC尝试握手标准PD协议（包括PD2.0/3.0Fixed PD3.0 PPS）对电池进行充电
	bool EnableSinkSCP;  		//是否让IC尝试握手华为协议（包括5A低压SCP 25W高压SCP和HSCP）对电池进行充电
	}IP2366SinkProtocolDef;	
	
typedef enum
	{
	TypeC_NoConnect=0x04,				
	TypeC_SourceOnly=0x01,  		
	TypeC_SinkOnly=0x00,		 	
	TypeC_Bidir=0x03	
	}TypeCRoleDef;	

typedef enum
	{
	VLow_2V5,
	VLow_2V6,
	VLow_2V7,
	VLow_2V8,
	VLow_2V9,
	VLow_3V0,
	VLow_3V1,
	VLow_3V2,
	}VBatLowDef;
	
typedef struct
	{
	float VBUSVolt;
	float VBUSCurrent;
  QuickChargeStateDef QuickChargeState;
	PDStateDef PDState;	 
	bool IsTypeCConnected;
	}IP2366VBUSStateDef;	
	
typedef struct	
	{
	bool IsEnable9VPDOSet;
	bool IsEnable12VPDOSet;
	bool IsEnable15VPDOSet;
	bool IsEnable20VPDOSet;
	int PDO9VICCMAX;  //9V PDO的电流设置
	int PDO12VICCMAX; //12V PDO的电流设置
	int PDO15VICCMAX; //15V PDO的电流设置
	int PDO20VICCMAX; //20V PDO的电流设置
	}IP2366FixPDOSetDef;

typedef struct
	{
	bool IsEnablePPS1Set;
	bool IsEnablePPS2Set;
	int PPS1Current;
	int PPS2Current;
	}IP2366PPSPDOSetDef;	
	
typedef struct
	{
	bool IsEnableOutput;  //开启对外输出功能
	bool IsEnablePDOut; //是否开启PD快充
	bool IsEnableDPDMOut; //是否开启高压快充协议
	bool IsEnableSCPOut; //是否开启SCP模式
	bool IsEnableHSCPOut; //开启高压SCP
	}IP2366OutConfigDef;

typedef struct
	{
	char FWID[5];
	int IP2366ICCMAX; //支持的最大电池端电流
	bool IsHSCPCapable; //是否支持HSCP对外Source
	bool IsExtendPDOCapable; //是否支持额外的PDO编辑
	ChargePowerDef MaxCapableChgPower; //最大支持的充电功率
	float ShuntValue; //检流电阻阻值
	bool IsHyperChargeCapable; //是否支持超充
	bool ExtendedROREGCapable; //是否支持额外的可读取寄存器（例如MFR_IC_VERSION和IC_TEMP）
	bool ExtendedTCSetting;    //固件是否支持额外的Type-C设置（例如Sink Power Set和Type-C Disconnect）  
	}IP2366FWCapDef;	
	
//电流回读参数配置
#define BusCurrentCalFactor 0.985	//IP2366读回来的电流修正值

	
//外部参考
extern const IP2366FWCapDef *CurrentIP2366FW;	
	
//特殊数值运算函数
bool IP2366_QueryCurrentStateIsACC(BatteryStateDef IN); //查询电池状态是否需要库仑计统计	
	
//函数
bool GetIfVBUSHasSinkVolt(void);	//获取VBUS是否有输入电压（该函数仅能在安全模式下使用）
void IP2366_DynamicUpdateVlow(VBatLowDef Vlow);	//根据系统充放电状态智能更新涓流电压的函数
bool IP2366_GetRecvPDOList(RecvPDOListDef *Result);	//获取输入广播的list状态
bool IP2366_UpdateSinkPower(ChargePowerDef Power); //更新系统的充电输入（Sink模式）的功率
bool IP2366_SetSinkProtocol(IP2366SinkProtocolDef *Cfg); //IP2366设置输入快充协议（不影响对外输出）
bool IP2366_SetInputState(IP2366InputDef * Cfg,bool IsSetChargePower); //设置系统输入配置
bool IP2366_DisableCharger(void); //禁止充电器
bool IP2366_GetChipTemp(char *TempOut,bool *IsTempLimitTriggered); //获取芯片本身的温度数据
IP2366HWRevDef IP2366_GetChipHWRev(void); //获取芯片的硬件版本号
bool IP2366_UpdateChipCap(char VendorString[5]); //获取芯片能力
bool IP2366_ForceEnterDeepSleep(void);		//IP2366强制进入低功耗睡眠模式
bool IP2366_SetDeepSleepModeEnabled(bool IsEnableSleep); //IP2366设置低功耗睡眠模式是否使能	
bool IP2366_GetIfCPortConnected(void);   //获取IP2366的C口是否已连接
bool IP2366_GetPPSCurrent(int *PPS1Current,int *PPS2Current);	//获取芯片PPS1和PPS2的输出电流
bool IP2366_SetFixedPDO(IP2366FixPDOSetDef *Cfg);	//设置固定模式PDO的输出电流（需要注意的是20V的PDO如果不是公版芯片不建议设置）
bool IP2366_SetPPSCurrent(IP2366PPSPDOSetDef *Cfg);	//设置芯片PPS1和PPS2的输出电流
bool IP2366_GetVRecharge(float *Vrecharge); //获取再充电电压
bool IP2366_getCurrentChargeParam(int *Istop,float *Vstop); //获取当前芯片的充电参数(浮充电压和停充电流等)
bool IP2366_GetCurrentPeakCurrent(int *Result); //获取峰值电流
bool IP2366_SetOTPSign(void); //设置重载检测标记
bool IP2366_DetectIfChipReset(bool *IsReset); //检查芯片是否复位
bool IP2366_SetVLowVolt(VBatLowDef Vlow); //设置低压保护
bool IP2366_GetFirmwareTimeStamp(char TimeStamp[5]);	//获取时间戳
bool IP2366_SetOutputState(IP2366OutConfigDef * CFG); //设置输出状态	
bool IP2366_GetRecvPDO(RecvPDODef *PDOResult);	//获取输入的PDO状态
bool IP2366_GetVBUSState(IP2366VBUSStateDef * State); //获取VBUS状态
bool IP2366_GetVBUSVoltage(float *VBUS);//获取C口VBUS的电压
bool IP2366_GetChargerState(BatteryStateDef *State);	//获取充电状态
bool IP2366_DetectIfPresent(void);	//监测IP2366是否存在
bool IP2366_SetTypeCRole(TypeCRoleDef Role); //设置TypeC的模式
bool IP2366_GetIfInputConnected(void);	//获取IP2366是否为输入连接
void IP2366_SetICCMax(int TargetCurrent); //反复设置iset寄存器直到电流一样为止
bool IP2366_ReadChipState(ChipStatDef *State);	//获取一部分芯片的信息
bool IP2366_SetPDOBroadCast(PDOBroadcastDef *PDOCfg);	//设置PDO广播
bool IP2366_EnableDCDC(bool IsEnableCharger,bool IsEnableDischarge); //配置充电器和放电	
bool IP2366_SetReChargeParam(ReChargeConfig Vrecharge,IStopConfig IStop); //设置再充电电流	
bool IP2366_UpdataChargePower(ChargePowerDef Power);	//更新充电功率
bool IP2366_UpdateFullVoltage(int Volt); //更新充电电压(传入的单位为mV)
void IP2366_ClearOCFlag(void); //清除OC Flag
void IP2366_LockUpDetect(void); //检测2366锁死

#endif
