redstoner-35/DFEx-FarBeaMon3tr/固件/驱动固件/Hardware/delay.c

/****************************************************************************/
/** \file delay.c
/** \Author redstoner_35
/** \Project Xtern Ripper Hyper Boost For GT96
/** \Description 这个文件负责实现系统中所需的等效8Hz心跳计时器和各种大小延时的处
理

**	History: Initial Release
**	
*****************************************************************************/
/****************************************************************************/
/*	include files
*****************************************************************************/
#include "cms8s6990.h"

/****************************************************************************/
/*	Local pre-processor symbols/macros('#define')
****************************************************************************/

/****************************************************************************/
/*	Global variable definitions(declared in header file with 'extern')
****************************************************************************/
volatile bit SysHFBitFlag; //高频心跳Flag(每62.5mS置1)
volatile bit LFStrobeFlag; //低频爆闪Flag(125mS)
volatile bit StrobeFlag; //高频爆闪Flag(62.5mS交替切换)

/****************************************************************************/
/*	Local variable definitions('static')
****************************************************************************/
static volatile bit IsT0OVF; //T0已溢出

/****************************************************************************/
/*	Interrupt Handler functions(Process Timer Interrupts)
****************************************************************************/

//启动系统调度模块的心跳定时器和阻塞延时
void StartSystemTimeBase(void)
	{
	//启动延时函数
	TCON=0x00; //清除溢出标记位，关闭定时器
	TMOD=0x01; //T0设置为使用Fext,16bit向上计数模式
	TH0=0x00;
	TL0=0x00; //初始化数值
	
	//配置T2心跳定时器模式			
  CCEN=0x00; //关闭比较和捕获
	RLDH=0x0B;
	RLDL=0xDB; //将重装载值设置为产生31.25mS延迟(1/32秒)，计算公式为65535-(48/24(0.5uS)=2000*31.25mS)=3035[0x0BDB]
	TH2=0x0B;
	TL2=0xDB;  //装载定时器初值，设定为0x0BDB使得定时器产生31.25mS延迟
	
	//启用中断
	T2IF=0x00; //清零T2中断
	T2IE=0x80; //令T2OVIE=1，启用T2 OVF中断
	IE=0xA2; //令ET0=1，ET2=1，分别启用T0和T2的定时中断,EA=1，启用全局总中断
	
	//复位flag并启动心跳定时器
	SysHFBitFlag=0;
  LFStrobeFlag=0;
	StrobeFlag=0;	 //复位所有flag
	T2CON=0x91; //设置T2时钟源为fSys/24=1MHz，定时器立即启动
	}

//系统心跳定时器的中断处理	
void Timer2_IRQHandler(void) interrupt TMR2_VECTOR
{ 
	T2IF=0x00; //清零T2中断
  //进行爆闪2分频
  StrobeFlag=~StrobeFlag; //TStrobe=31.25*2=62.5mS
	if(StrobeFlag)
		{
		SysHFBitFlag=1;  //每62.5mS将flag置1
		LFStrobeFlag=~LFStrobeFlag; //翻转低频爆闪flag
		}
}		
	
//软件延时定时器的中断处理
void Timer0_IRQHandler(void) interrupt TMR0_VECTOR  //0x0B 
{
  TCON&=0xEF; //清除溢出标记位
	IsT0OVF=1;
} 	

//1ms延时
void delay_ms(int ms)
	{
	unsigned long CNT;
	unsigned char repcounter=0;
	//计算定时器重装值
	if(ms==0)return;
  do
	  {
		repcounter++; //重复计数器+1
		CNT=(long)ms*4000; //T0一个周期是48/12=4MHz=0.25uS
		CNT/=(long)repcounter; //除以重复次数得到单次计数值
		}
  while(CNT>0xFFFF); //反复循环确保定时器值小于65535
	CNT=0xFFFF-CNT; //计算结束，将16bit计数器满的值加载到定时器内
	//开始进行单次或多次倒计时
	do
		{			
		//装载定时器值
		TH0=(CNT>>8)&0xFF;
	  TL0=CNT&0xFF; 
		IsT0OVF=0; //复位标志位
		//启动定时器开始倒计时
		TCON|=0x10; //TR0=1,定时器开始计时	
		while(!(TCON&0x20)&&!IsT0OVF); //等待直到T0溢出
		//计时结束，准备进行下一轮
		TCON&=0xCF; //清除溢出标记位，关闭定时器
		repcounter--; //重复次数-1
		}
	while(repcounter);
	}
/*************************  End Of File  ***********************/
