redstoner-35/DFEx-FarBeaMon3tr/固件/电池棒控制器固件/Hardware/I2CDrv.c

#include "ht32.h"
#include "I2C.h"
#include "delay.h"
#include "GUI.h"
#include <string.h>
#include "I2CAddr.h"

//内部设备地址列表
const char I2CSlaveADDR[]={IP2366ADDR,M24C512ADDR,M24C512SecuADDR};
unsigned char SMIOADDR=0; //SMBUS IO扩展器的地址

//I2C延时
#define IIC_delay() delay_us(3)

//static void IIC_delay(void)
//  {
//	int i=255;
//	while(--i);
//	}

//报告异常从机地址
static void ReportFailedSlave(char Addr)
	{
	char FaultADDRINFO[32];
	ShowPostInfo(16,"从机通信异常\0","W2",Msg_Warning);
	delay_Second(1);
	memset(FaultADDRINFO,0,sizeof(FaultADDRINFO));
	snprintf(FaultADDRINFO,32,"异常地址:0x%02X",Addr);
	ShowPostInfo(16,FaultADDRINFO,"W2",Msg_Warning);
	}

//SMBUS初始化
void SMBUS_Init(void)
  {
	 char i;
	 
	 ShowPostInfo(16,"启动SMBUS控制器\0","06",Msg_Statu);
	 //配置GPIO(SCL)
   AFIO_GPxConfig(IIC_SCL_IOB,IIC_SCL_IOP, AFIO_FUN_GPIO);//I2C SCL(用来做时钟)
   GPIO_DirectionConfig(IIC_SCL_IOG,IIC_SCL_IOP,GPIO_DIR_OUT);//配置为输出
   GPIO_SetOutBits(IIC_SCL_IOG,IIC_SCL_IOP);//输出设置为1
	 GPIO_PullResistorConfig(IIC_SCL_IOG,IIC_SCL_IOP,GPIO_PR_UP);//启用上拉
	 //配置GPIO(SDA)
   AFIO_GPxConfig(IIC_SDA_IOB,IIC_SDA_IOP, AFIO_FUN_GPIO);//I2C SDA(用来做数据)
   GPIO_DirectionConfig(IIC_SDA_IOG,IIC_SDA_IOP,GPIO_DIR_OUT);//配置为输出
   GPIO_SetOutBits(IIC_SDA_IOG,IIC_SDA_IOP);//输出设置为1	 
	 GPIO_PullResistorConfig(IIC_SDA_IOG,IIC_SDA_IOP,GPIO_PR_UP);//启用上拉
	 //测试slave
	 for(i=0;i<sizeof(I2CSlaveADDR);i++)
			{
			IIC_Start();
			IIC_Send_Byte(I2CSlaveADDR[i]);
			if(IIC_Wait_Ack())ReportFailedSlave(I2CSlaveADDR[i]);
			delay_us(60);
			IIC_Stop();
			delay_ms(1);
			}
	//尝试和8bit的GPIO扩展器进行握手
	IIC_Start();
	IIC_Send_Byte(ADVSMIOADDR);
	if(!IIC_Wait_Ack())SMIOADDR=ADVSMIOADDR;
	delay_us(60);
	IIC_Stop();
	if(SMIOADDR==ADVSMIOADDR)return; //高级扩展器存在且协商成功，进入处理		
	//高级扩展器协商失败，检查4bit的扩展器是否存在
	delay_ms(1);
	SMIOADDR=OLDSMIOADDR; //设置IO扩展器的地址数据
	IIC_Start();
	IIC_Send_Byte(OLDSMIOADDR);	
	if(!IIC_Wait_Ack())ReportFailedSlave(OLDSMIOADDR);	
	delay_us(60);
	IIC_Stop();
	}

//设置传输方向
static void SetTransferDir(BDIR DIR)
  {
	GPIO_DirectionConfig(IIC_SDA_IOG,IIC_SDA_IOP,(DIR==SMBUS_DIR_MOTS)?GPIO_DIR_OUT:GPIO_DIR_IN);//配置IO方向
	GPIO_InputConfig(IIC_SDA_IOG,IIC_SDA_IOP,(DIR==SMBUS_DIR_MOTS)?DISABLE:ENABLE);//启用或禁用IDR
	}
//产生IIC起始信号
void IIC_Start(void)
{
	SetTransferDir(SMBUS_DIR_MOTS);//主机->从机
	IIC_SDA_Set();	  	  
	IIC_SCL_Set();
	IIC_delay();
 	IIC_SDA_Clr();//START:when CLK is high,DATA change form high to low 
	IIC_delay();
	IIC_SCL_Clr();//钳住I2C总线，准备发送或接收数据 
}	  
//产生IIC停止信号
void IIC_Stop(void)
{
	SetTransferDir(SMBUS_DIR_MOTS);//主机->从机
	IIC_SCL_Clr();
	IIC_SDA_Clr();//STOP:when CLK is high DATA change form low to high
 	IIC_delay();
	IIC_SCL_Set(); 
	IIC_delay();
	IIC_SDA_Set();//发送I2C总线结束信号
	IIC_delay();							   	
}
//等待应答信号到来
//返回值：1，接收应答失败
//        0，接收应答成功
char IIC_Wait_Ack(void)
{
	u8 ucErrTime=0;
	IIC_SDA_Set();//释放数据线
	IIC_delay();	   
	IIC_SCL_Set();//时钟拉高
	IIC_delay();	
	SetTransferDir(SMBUS_DIR_SOTM);//从机->主机
	while(READ_SDA)
	{
		ucErrTime++;
		IIC_delay();
		if(ucErrTime>250)
		{
			IIC_Stop();
			return 1;
		}
	}
	IIC_SCL_Clr();//时钟输出0 	   
	return 0;  
} 
//产生ACK应答
void IIC_Ack(void)
{
	SetTransferDir(SMBUS_DIR_MOTS);//主机->从机
	IIC_SCL_Clr();
	IIC_SDA_Clr();
	IIC_delay();
	IIC_SCL_Set();
	IIC_delay();
	IIC_SCL_Clr();
}
//不产生ACK应答		    
void IIC_NAck(void)
{
	SetTransferDir(SMBUS_DIR_MOTS);//主机->从机
	IIC_SCL_Clr();
	IIC_SDA_Set();
	IIC_delay();
	IIC_SCL_Set();
	IIC_delay();
	IIC_SCL_Clr();
}					 				     
//IIC发送一个字节	  
void IIC_Send_Byte(unsigned char txd)
{                        
    u8 t;      
	  SetTransferDir(SMBUS_DIR_MOTS);//主机->从机
    IIC_SCL_Clr();//拉低时钟开始数据传输
    IIC_delay();//等一等再开始传输
    for(t=0;t<8;t++)
    {              
    if(txd&0x80)IIC_SDA_Set();
		else IIC_SDA_Clr();
    txd<<=1; 	  
		IIC_delay();   //对TEA5767这三个延时都是必须的
		IIC_SCL_Set();
		IIC_delay(); 
		IIC_SCL_Clr();	
		IIC_delay();
    }	 
} 	    
//读1个字节，ack=1时，发送ACK，ack=0，发送nACK   
unsigned char IIC_Read_Byte(unsigned char ack)
{
	unsigned char i,receive=0;
	  IIC_SDA_Set();//释放总线
	  SetTransferDir(SMBUS_DIR_SOTM);//从机->主机
    for(i=0;i<8;i++ )
	{
        IIC_SCL_Clr(); 
        IIC_delay();
		    IIC_SCL_Set();
        receive<<=1;
        if(READ_SDA)receive++;   
		    IIC_delay(); 
    }					 
    if (!ack)
        IIC_NAck();//发送nACK
    else
        IIC_Ack(); //发送ACK   
    return receive;
}
